Catmacey/ChipStomp/Bootloader/BoardConfig.h

/************************************************************************/
/*                                                                      */
/*    BoardConfig.h   This configures board specific features           */
/*                  for the stk500v2 avrdude/MPIDE PIC32                */
/*                    compliment bootloader                             */
/*                                                                      */
/************************************************************************/
/*    Author:     Keith Vogel                                           */
/*  Copyright 2013, Digilent Inc.                                       */
/************************************************************************/
/*
*
* Copyright (c) 2013-2014, Digilent <www.digilentinc.com>
* Contact Digilent for the latest version.
*
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
* THIS SOFTWARE IS PROVIDED BY THE COPYRIGHT HOLDERS AND CONTRIBUTORS "AS IS" AND
* ANY EXPRESS OR IMPLIED WARRANTIES, INCLUDING, BUT NOT LIMITED TO, THE IMPLIED
* WARRANTIES OF MERCHANTABILITY AND FITNESS FOR A PARTICULAR PURPOSE ARE DISCLAIMED.
* IN NO EVENT SHALL THE COPYRIGHT OWNER OR CONTRIBUTORS BE LIABLE FOR ANY DIRECT,
* INDIRECT, INCIDENTAL, SPECIAL, EXEMPLARY, OR CONSEQUENTIAL DAMAGES (INCLUDING,
* BUT NOT LIMITED TO, PROCUREMENT OF SUBSTITUTE GOODS OR SERVICES; LOSS OF USE,
* DATA, OR PROFITS; OR BUSINESS INTERRUPTION) HOWEVER CAUSED AND ON ANY THEORY OF
* LIABILITY, WHETHER IN CONTRACT, STRICT LIABILITY, OR TORT (INCLUDING NEGLIGENCE
* OR OTHERWISE) ARISING IN ANY WAY OUT OF THE USE OF THIS SOFTWARE, EVEN IF ADVISED
* OF THE POSSIBILITY OF SUCH DAMAGE.
*/
/************************************************************************/
/*  Revision History:                                                   */
/*                                                                      */
/*    2/23/2011(KeithV): Created                                        */
/*    6/17/2012(KeithV): Added Just In Time Flash Erase                 */
/*    6/17/2012(KeithV): Added header information                       */
/*    6/25/2012(KeithV): Added Vendor ID and Product IDs                */
/*    1/15/2013(BrianS): Added PPS unlock for MX1/MX2 devices           */
/*    3/18/2013(BrianS): Added 48Mhz FB Mini device, fixed USBID and    */
/*                       VBUSON                                         */
/*    22/5/2013(gmtii):  Added Olimex PIC32 Pinguino board		        */
/*    6/2302/13(BrianS): Added DP32                                     */
/*    1/15/2014 (KeithV): Added MZ support                              */
/*                                                                      */
/************************************************************************/

// *****************************************************************************
// *****************************************************************************
//                     Helper Macros
// *****************************************************************************
// *****************************************************************************
#define CAT1_2(a,b)         a##b
#define CAT_2(a,b)          CAT1_2(a,b)
#define CAT_3(a,b,c)        CAT_2(CAT_2(a,b),c)
#define CAT_4(a,b,c,d)      CAT_2(CAT_2(a,b),CAT_2(c,d))
#define CAT_5(a,b,c,d,e)    CAT_2(CAT_3(a,b,c),CAT_2(d,e))
#define Low     0
#define High    1

// *****************************************************************************
// *****************************************************************************
//                     Vendor IDs
// *****************************************************************************
// *****************************************************************************
#define     vendUnknown         0xFFFF
#define     vendUnassigned      0x0000
#define     vendDigilent        0x0001
#define     vendMicrochip       0x0002
#define     vendFubarino        0x0003
#define     vendSchmalzHausLLC  0x0004
#define     vendOlimex          0x0005
#define		vendElement14		0x0006
#define     vendPontech         0x0007
#define     vendExperimental    0x8000

// *****************************************************************************
// *****************************************************************************
//                    Digilent Product IDs
// *****************************************************************************
// *****************************************************************************
#define     prodUnknown         0xFFFF
#define     prodUnassigned      0x0000

// Hardware / software Arduino compatible chipKITs
#define     prodChipKITUno32    0x0101
#define     prodChipKITMax32    0x0102
#define     prodChipKITuC32     0x0103
#define     prodChipKITWF32     0x0104
#define     prodChipKITFG32     0x0105

// Cerebot like boards, only software Arduino compatible chipKITs
#define     prodCerebot32MX4    0x0201
#define     prodCerebot32MX7    0x0202
#define     prodCerebotMX3cK128 0x0203
#define     prodCerebotMX4cK    0x0204
#define     prodCerebotMX7cK    0x0205
#define     prodCerebotMX3cK512 0x0206

// DIP form factor, only software Arduino compatible chipKITs
#define     prodCmodCK1         0x0301

// Experimenter boards form factor, only software Arduino compatible chipKITs
#define     prodChipKITDP32     0x0401

// UDB board
#define     prodChipKITUDB32PIM 0x0501

// MZ processors
#define     prodChipKITWiFire   0x0601
#define     prodChipKITzUno     0x0602


// *****************************************************************************
// *****************************************************************************
//                    Fubarino Product IDs
// *****************************************************************************
// *****************************************************************************
#define     prodFubarinoSD      0x0001
#define     prodFubarinoMini    0x0002
#define     prodFubarinoSD_512K 0x0003
#define     prodFubarinoMini48MHz 0x0004
#define     prodFubarinoMini50MHz 0x0005

// *****************************************************************************
// *****************************************************************************
//                    Schmalz Haus Product IDs
// *****************************************************************************
// *****************************************************************************
#define     prodEBBv3      		0x0001
#define     prodUBW32MX460 		0x0002
#define     prodUBW32MX795 		0x0003

// *****************************************************************************
// *****************************************************************************
//                    Olimex Product IDs
// *****************************************************************************
// *****************************************************************************
#define     prodOlimex_PIC32_Pinguino   0x0001
#define     prodOlimex_Duinomite        0x0002

// *****************************************************************************
// *****************************************************************************
//                    Element14 Product IDs
// *****************************************************************************
// *****************************************************************************
#define     prodChipkitPi		0x0001

// *****************************************************************************
// *****************************************************************************
//                    Pontech Product IDs
// *****************************************************************************
// *****************************************************************************
#define     prodQuick240                0x0001

// Bootloader Capability bits
// The first 4 bits define what type of STK500 interface is used
// The next 4 bits define what LEDs are used
// The next 8 bits define how the bootloader is to be put in programming/listen mode
// The next 8 bits are how flash is erased instructed by the linker
// The next 4 bits are this and that capabilities instructed by the linker
// The last 4 bits are this and that capabilities
#define blCapUARTInterface                              0x00000001ul        // Avrdude talks over a UART
#define blCapUSBInterface                               0x00000002ul        // Avrdude talks over the USB for serial
#define blCapBootLED                                    0x00000010ul        // A boot LED is driven
#define blCapDownloadLED                                0x00000020ul        // A download LED is driven
#define blCapAutoResetListening                         0x00000100ul        // There is a short listening delay after reset for avrdude to upload a sketch before automatically loading the in flash sketch              
#define blCapProgramButton                              0x00000200ul        // A program button is suppored  
#define blCapVirtualProgramButton                       0x00000400ul        // A virtual program button is suppored
#define blCapLkInstrFullFlashEraseLess4KEEProm          0x00010000ul        // The original bootloader method of erasing all of program flash except the last 4K reserved for eeprom
#define blCapLkInstrJustInTimeFlashErase                0x00020000ul        // Only flash pages written too needed by the sketch is erased
#define blCapLkInstrFlashErase                          0x00040000ul        // The linker defines the flash range to erase
#define blCapLkInstrFullFlashErase                      0x00080000ul        // All of flash is erased
#define blCapLkInstrExecutionJumpAddress                0x01000000ul        // the bootloader will jump to the execution jump address immediately after programming
#define blCapLkInstrExecutionJumpToFirstInFlash         0x02000000ul        // the bootloader will jump to the first sketch loaded in flash ignoring the execution jump address immediately after programming
#define blCapSupportsRamHeaderAndPersistentData         0x10000000ul        // This checks and clears the Ram Header and adds RAM header data like the RCON value
#define blCapSplitFlashBootloader                       0x20000000ul        // This is a split flash bootloader with some of the bootloader in program flash
#define blCapSmartStart                                 0x40000000ul        // To indicate that the bootloader has implemented a smart start sequence to prevent execution of the sketch until all start sequences have stabalized.
#define blCapNotProvided                                0x80000000ul        // If this is set, then all capability bits have no meaning. This will be set if flash is in its erased state and the bootloader did not set any bits.

#define CAPCOMMON (blCapLkInstrFullFlashEraseLess4KEEProm | blCapLkInstrJustInTimeFlashErase | blCapLkInstrFlashErase | blCapLkInstrFullFlashErase | blCapLkInstrExecutionJumpAddress | blCapLkInstrExecutionJumpToFirstInFlash | blCapSupportsRamHeaderAndPersistentData)

#if !defined(__PIC32MX__) && !defined(__PIC32MZ__)
    #error "This project was designed for PIC32MX family devices. Please select the appropriate project for your target device family."
#endif

// For historical reasons, these must be defined as these specific constants and nothing else
#define FLASH_START             0x9D000000
#define USER_APP_ADDR           0x9D001000
#define DEFAULT_EEPROM_SIZE     4096

//************************************************************************
#if defined(_BOARD_EXAMPLE_MX1_)               

#if defined(PUT_CONFIG_BITS_HERE)

    //*    Oscillator Settings
    #pragma config FNOSC    = PRIPLL                        // Oscillator Selection
    #pragma config POSCMOD  = XT                            // Primary Oscillator
    #pragma config FPLLIDIV = DIV_2                         // PLL input divider
    #pragma config FPLLMUL  = MUL_20                        // PLL multiplier
    #pragma config FPLLODIV = DIV_2                         // PLL output divider
    #pragma config FPBDIV   = DIV_1                         // Peripheral bus clock divider
    #pragma config FSOSCEN  = OFF                           // Secondary Oscillator Enable

    //*    Clock control settings
    #pragma config IESO     = ON                            // Internal/External Switch-over
    #pragma config FCKSM    = CSDCMD                        // Clock Switching & Fail Safe Clock Monitor
    #pragma config OSCIOFNC = OFF                           // CLKO Enable

    //*    Other Peripheral Device settings
    #pragma config FWDTEN   = OFF                           // Watchdog Timer
    #pragma config WDTPS    = PS1024                        // Watchdog Timer Postscale
    #pragma config WINDIS   = OFF
    #pragma config JTAGEN   = OFF                           // JTAG port disabled

    //*    Code Protection settings
    #pragma config CP       = OFF                           // Code Protect
    #pragma config BWP      = OFF                           // Boot Flash Write Protect
    #pragma config PWP      = OFF                           // Program Flash Write Protect

    //*    Debug settings
    #pragma config ICESEL   = ICS_PGx1                      // ICE/ICD Comm Channel Select
    //#pragma config DEBUG    = ON                          // DO NOT SET THIS CONFIG BIT, it will break debugging

    #pragma config PMDL1WAY = OFF                           // Allow multiple reconfigurations
    #pragma config IOL1WAY  = OFF                           // Allow multiple reconfigurations
#endif

    #define CAPABILITIES    (blCapBootLED | blCapDownloadLED | blCapUARTInterface | blCapProgramButton | blCapVirtualProgramButton | CAPCOMMON)

    // BTN / LED sense
    #define LedOn       High
    #define BntOn       High

    // Boot LED
    #define BLedLat     A
    #define BLedBit     7

    // Download LED
    #define DLedLat     A
    #define DLedBit     8

    // Virtual program button
    #define VPBntLat    A
    #define VPBntBit    4

    // Program button
    #define PBntPort    A
    #define PBntBit     4

    #define _CPU_NAME_              "32MX120F032D"
    #define VEND                    vendUnassigned
    #define PROD                    prodUnassigned
    #define F_CPU                   40000000UL              // CPU frequence
    #define F_PBUS                  F_CPU                   // Peripheral bus rate F_CPU / FPBDIV; just set it, saves code.

    #define FLASH_BYTES             0x8000                  // 32K
    #define FLASH_PAGE_SIZE         1024

    #define BOOTLOADER_UART         1                       // avrdude program UART
    #define BAUDRATE                115200                  // avrdude baudrate
    #define UARTMapRX()             (U1RXR = 0x1)           // RPB6 -> U1RX
    #define UARTMapTX()             (RPB7R = 0x1)           // RB7 -> U1TX
 
//************************************************************************
#elif defined(_BOARD_UDB32_MX2_DIP_)

#if defined(PUT_CONFIG_BITS_HERE)

    //* Oscillator Settings
    #pragma config FNOSC    = PRIPLL                                // Oscillator selection
    #pragma config POSCMOD  = XT                                    // Primary oscillator mode
    #pragma config FPLLIDIV = DIV_2                                 // PLL input divider
    #pragma config FPLLMUL  = MUL_20                                // PLL multiplier
    #pragma config FPLLODIV = DIV_2                                 // PLL output divider
    #pragma config FPBDIV   = DIV_1                                 // Peripheral bus clock divider
    #pragma config FSOSCEN  = OFF                                    // Secondary oscillator enable

    //* Clock control settings
    #pragma config IESO     = OFF                                   // Internal/external clock switchover
    #pragma config FCKSM    = CSECME                                // Clock switching (CSx)/Clock monitor (CMx)
    #pragma config OSCIOFNC = OFF                                   // Clock output on OSCO pin enable

    //* USB Settings
    #pragma config UPLLEN   = ON                                    // USB PLL enable
    #pragma config UPLLIDIV = DIV_2                                 // USB PLL input divider
    #pragma config FVBUSONIO = OFF                                  // Make VBUSON a GPIO pin
    #pragma config FUSBIDIO = OFF                                   // Controlled by port function

    //* Other Peripheral Device settings
    #pragma config FWDTEN   = OFF                                   // Watchdog timer enable
    #pragma config WDTPS    = PS1024                                // Watchdog timer postscaler
    #pragma config WINDIS   = OFF
    #pragma config JTAGEN   = OFF                                   // JTAG port disabled

    //* Code Protection settings
    #pragma config CP       = OFF                                   // Code protection
    #pragma config BWP      = OFF                                   // Boot flash write protect
    #pragma config PWP      = OFF                                   // Program flash write protect

    //*    Debug settings
    #pragma config ICESEL   = ICS_PGx1                      		// ICE/ICD Comm Channel Select
    //#pragma config DEBUG    = ON                          		// DO NOT SET THIS CONFIG BIT, it will break debugging

    #pragma config PMDL1WAY = OFF                           		// Allow multiple reconfigurations
    #pragma config IOL1WAY  = OFF                           		// Allow multiple reconfigurations
#endif

    #define CAPABILITIES    (blCapBootLED | blCapDownloadLED | blCapUARTInterface | blCapProgramButton | blCapVirtualProgramButton | CAPCOMMON)

    // BTN / LED sense
    #define LedOn       Low
    #define BntOn       High

    // Boot LED
    #define BLedLat     B
    #define BLedBit     0

    // Download LED
    #define DLedLat     B
    #define DLedBit     1

    // Virtual program button
    #define VPBntLat    B
    #define VPBntBit    4

    // Program button
    #define PBntPort    B
    #define PBntBit     4

    #define _CPU_NAME_                  "32MX250F128B"
    #define VEND                        vendDigilent
    #define PROD                        prodChipKITDP32
    #define F_CPU                       40000000UL
    #define F_PBUS                      F_CPU

    #define FLASH_BYTES                 (0x20000)           // Leave room 4 pages (for bootloader!)
    #define FLASH_PAGE_SIZE             1024                // In bytes

    #define BOOTLOADER_UART             1                   // avrdude program UART
    #define BAUDRATE                    115200              // avrdude baudrate
    #define UARTMapRX()                 (U1RXR = 0x3)       // RPB13 -> U1RX
    #define UARTMapTX()                 (RPB3R = 0x1)       // RB3 -> U1TX

//************************************************************************
#elif defined(_BOARD_CMOD_CK1_)

#if defined(PUT_CONFIG_BITS_HERE)

    //*    Oscillator Settings
    #pragma config FNOSC    = PRIPLL                        // Oscillator Selection
    #pragma config POSCMOD  = XT                            // Primary Oscillator
    #pragma config FPLLIDIV = DIV_2                         // PLL input divider
    #pragma config FPLLMUL  = MUL_20                        // PLL multiplier
    #pragma config FPLLODIV = DIV_2                         // PLL output divider
    #pragma config FPBDIV   = DIV_1                         // Peripheral bus clock divider
    #pragma config FSOSCEN  = OFF                           // Secondary Oscillator Enable

    //*    Clock control settings
    #pragma config IESO     = ON                            // Internal/External Switch-over
    #pragma config FCKSM    = CSDCMD                        // Clock Switching & Fail Safe Clock Monitor
    #pragma config OSCIOFNC = OFF                           // CLKO Enable

    //*    Other Peripheral Device settings
    #pragma config FWDTEN   = OFF                           // Watchdog Timer
    #pragma config WDTPS    = PS1024                        // Watchdog Timer Postscale
    #pragma config WINDIS   = OFF
    #pragma config JTAGEN   = OFF                           // JTAG port disabled

    //*    Code Protection settings
    #pragma config CP       = OFF                           // Code Protect
    #pragma config BWP      = OFF                           // Boot Flash Write Protect
    #pragma config PWP      = OFF                           // Program Flash Write Protect

    //*    Debug settings
    #pragma config ICESEL   = ICS_PGx2                      // ICE/ICD Comm Channel Select
    //#pragma config DEBUG    = ON                          // DO NOT SET THIS CONFIG BIT, it will break debugging

    #pragma config PMDL1WAY = OFF                           // Allow multiple reconfigurations
    #pragma config IOL1WAY  = OFF                           // Allow multiple reconfigurations
#endif

    #define CAPABILITIES    (blCapBootLED | blCapDownloadLED | blCapUARTInterface | blCapAutoResetListening | blCapVirtualProgramButton | CAPCOMMON)

    // BTN / LED sense
    #define LedOn       High
    #define BntOn       High

    // Boot LED
    #define BLedLat     A
    #define BLedBit     10

    // Download LED
    #define DLedLat     B
    #define DLedBit     12

    // Virtual program button
    #define VPBntLat    A
    #define VPBntBit    2

    #define _CPU_NAME_              "PIC32MX150F128D"
    #define VEND                    vendDigilent
    #define PROD                    prodCmodCK1
    #define F_CPU                   40000000UL              // CPU frequence
    #define F_PBUS                  F_CPU                   // Peripheral bus rate F_CPU / FPBDIV; just set it, saves code.

    #define FLASH_BYTES             0x20000                  // 128K
    #define FLASH_PAGE_SIZE         1024

    #define LISTEN_BEFORE_LOAD      2000                    // no less than 2 seconds
    #define BOOTLOADER_UART         1                       // avrdude program UART
    #define BAUDRATE                115200                  // avrdude baudrate
    #define UARTMapRX()             (U1RXR = 0x5)           // RPC6 -> U1RX
    #define UARTMapTX()             (RPB3R = 0x1)           // RPB3 -> U1TX

//************************************************************************
#elif defined(_BOARD_CHIPKIT_DP32_)

#if defined(PUT_CONFIG_BITS_HERE)

    //* Oscillator Settings
    #pragma config FNOSC    = PRIPLL                                // Oscillator selection
    #pragma config POSCMOD  = XT                                    // Primary oscillator mode
    #pragma config FPLLIDIV = DIV_2                                 // PLL input divider
    #pragma config FPLLMUL  = MUL_20                                // PLL multiplier
    #pragma config FPLLODIV = DIV_2                                 // PLL output divider
    #pragma config FPBDIV   = DIV_1                                 // Peripheral bus clock divider
    #pragma config FSOSCEN  = OFF                                    // Secondary oscillator enable

    //* Clock control settings
    #pragma config IESO     = OFF                                   // Internal/external clock switchover
    #pragma config FCKSM    = CSECME                                // Clock switching (CSx)/Clock monitor (CMx)
    #pragma config OSCIOFNC = OFF                                   // Clock output on OSCO pin enable

    //* USB Settings
    #pragma config UPLLEN   = ON                                    // USB PLL enable
    #pragma config UPLLIDIV = DIV_2                                 // USB PLL input divider
    #pragma config FVBUSONIO = OFF                                  // Make VBUSON a GPIO pin
    #pragma config FUSBIDIO = OFF                                   // Controlled by port function

    //* Other Peripheral Device settings
    #pragma config FWDTEN   = OFF                                   // Watchdog timer enable
    #pragma config WDTPS    = PS1024                                // Watchdog timer postscaler
    #pragma config WINDIS   = OFF
    #pragma config JTAGEN   = OFF                                   // JTAG port disabled

    //* Code Protection settings
    #pragma config CP       = OFF                                   // Code protection
    #pragma config BWP      = OFF                                   // Boot flash write protect
    #pragma config PWP      = OFF                                   // Program flash write protect

    //*    Debug settings
    #pragma config ICESEL   = ICS_PGx1                      		// ICE/ICD Comm Channel Select
    //#pragma config DEBUG    = ON                          		// DO NOT SET THIS CONFIG BIT, it will break debugging

    #pragma config PMDL1WAY = OFF                           		// Allow multiple reconfigurations
    #pragma config IOL1WAY  = OFF                           		// Allow multiple reconfigurations
#endif

    #define CAPABILITIES    (blCapBootLED | blCapDownloadLED | blCapSplitFlashBootloader | blCapUSBInterface | blCapProgramButton | blCapVirtualProgramButton | CAPCOMMON)

    // BTN / LED sense
    #define LedOn       High
    #define BntOn       High

    // Boot LED
    #define BLedLat     B
    #define BLedBit     3

    // Download LED
    #define DLedLat     B
    #define DLedBit     2

    // Virtual program button
    #define VPBntLat    B
    #define VPBntBit    4

    // Program button
    #define PBntPort    B
    #define PBntBit     4

    #define _CPU_NAME_                  "32MX250F128B"
    #define VEND                        vendDigilent
    #define PROD                        prodChipKITDP32
    #define F_CPU                       40000000UL
    #define F_PBUS                      F_CPU

    #define FLASH_BYTES                 (0x20000-0x1000)		    // Leave room 4 pages (for bootloader!)
    #define FLASH_PAGE_SIZE             1024                                // In bytes

//************************************************************************
#elif defined(_BOARD_CHIPKIT_DP32_CHIPSTOMP_)

#if defined(PUT_CONFIG_BITS_HERE)

    //* Oscillator Settings
    #pragma config FNOSC    = PRIPLL                                // Oscillator selection
    #pragma config POSCMOD  = XT                                    // Primary oscillator mode
    #pragma config FPLLIDIV = DIV_2                                 // PLL input divider
    #pragma config FPLLMUL  = MUL_20                                // PLL multiplier
    #pragma config FPLLODIV = DIV_2                                 // PLL output divider
    #pragma config FPBDIV   = DIV_1                                 // Peripheral bus clock divider
    #pragma config FSOSCEN  = OFF                                    // Secondary oscillator enable

    //* Clock control settings
    #pragma config IESO     = OFF                                   // Internal/external clock switchover
    #pragma config FCKSM    = CSECME                                // Clock switching (CSx)/Clock monitor (CMx)
    #pragma config OSCIOFNC = OFF                                   // Clock output on OSCO pin enable

    //* USB Settings
    #pragma config UPLLEN   = ON                                    // USB PLL enable
    #pragma config UPLLIDIV = DIV_2                                 // USB PLL input divider
    #pragma config FVBUSONIO = OFF                                  // Make VBUSON a GPIO pin
    #pragma config FUSBIDIO = OFF                                   // Controlled by port function

    //* Other Peripheral Device settings
    #pragma config FWDTEN   = OFF                                   // Watchdog timer enable
    #pragma config WDTPS    = PS1024                                // Watchdog timer postscaler
    #pragma config WINDIS   = OFF
    #pragma config JTAGEN   = OFF                                   // JTAG port disabled

    //* Code Protection settings
    #pragma config CP       = OFF                                   // Code protection
    #pragma config BWP      = OFF                                   // Boot flash write protect
    #pragma config PWP      = OFF                                   // Program flash write protect

    //*    Debug settings
    #pragma config ICESEL   = ICS_PGx1                              // ICE/ICD Comm Channel Select
    //#pragma config DEBUG    = ON                                  // DO NOT SET THIS CONFIG BIT, it will break debugging

    #pragma config PMDL1WAY = OFF                                   // Allow multiple reconfigurations
    #pragma config IOL1WAY  = OFF                                   // Allow multiple reconfigurations
#endif

    #define CAPABILITIES    (blCapBootLED | blCapDownloadLED | blCapSplitFlashBootloader | blCapUSBInterface | blCapProgramButton | blCapVirtualProgramButton | CAPCOMMON)

    // BTN / LED sense
    #define LedOn       High
    #define BntOn       Low

    // Boot LED
    #define BLedLat     B
    #define BLedBit     3

    // Download LED
    #define DLedLat     B
    #define DLedBit     2

    // Virtual program button
    #define VPBntLat    B
    #define VPBntBit    4

    // Program button
    #define PBntPort    B
    #define PBntBit     4

    #define _CPU_NAME_                  "32MX250F128B"
    #define VEND                        vendDigilent
    #define PROD                        prodChipKITDP32
    #define F_CPU                       40000000UL
    #define F_PBUS                      F_CPU

    #define FLASH_BYTES                 (0x20000-0x1000)            // Leave room 4 pages (for bootloader!)
    #define FLASH_PAGE_SIZE             1024                                // In bytes

//************************************************************************
#elif defined(_BOARD_CHIPKIT_UNO32_)

#if defined(PUT_CONFIG_BITS_HERE)

    //*    Oscillator Settings
    #pragma config FNOSC    = PRIPLL                        // Oscillator selection
    #pragma config POSCMOD  = XT                            // Primary oscillator mode
    #pragma config FPLLIDIV = DIV_2                         // PLL input divider
    #pragma config FPLLMUL  = MUL_20                        // PLL multiplier
    #pragma config FPLLODIV = DIV_1                         // PLL output divider
    #pragma config FPBDIV   = DIV_1                         // Peripheral bus clock divider
    #pragma config FSOSCEN  = ON                            // Secondary oscillator enable

    //*    Clock control settings
    #pragma config IESO     = OFF                           // Internal/external clock switchover
    #pragma config FCKSM    = CSDCMD                        // Clock switching (CSx)/Clock monitor (CMx)
    #pragma config OSCIOFNC = OFF                           // Clock output on OSCO pin enable

    //*    Other Peripheral Device settings
    #pragma config FWDTEN   = OFF                           // Watchdog timer enable
    #pragma config WDTPS    =  PS1024                       // Watchdog timer postscaler

    //*    Code Protection settings
    #pragma config CP       = OFF                           // Code protection
    #pragma config BWP      = OFF                           // Boot flash write protect
    #pragma config PWP      = OFF                           // Program flash write protect

    //*    Debug settings
    #pragma config ICESEL   = ICS_PGx2                      // ICE pin selection
#endif

    #define CAPABILITIES    (blCapBootLED | blCapDownloadLED | blCapUARTInterface | blCapAutoResetListening | blCapVirtualProgramButton | CAPCOMMON)

    // BTN / LED sense
    #define LedOn       High
    #define BntOn       High

    // Boot LED
    #define BLedLat     G
    #define BLedBit     6

    // Download LED
    #define DLedLat     F
    #define DLedBit     0

    // Virtual program button
    #define VPBntLat    C
    #define VPBntBit    12

    // Other capabilities
    #define LISTEN_BEFORE_LOAD          2000                // no less than 2 seconds
    #define BOOTLOADER_UART             1                   // avrdude program UART
    #define BAUDRATE                    115200              // avrdude baudrate
 
    #define _CPU_NAME_                  "32MX320F128H"
    #define VEND                        vendDigilent
    #define PROD                        prodChipKITUno32
    #define F_CPU                       80000000UL
    #define F_PBUS                      F_CPU

    #define FLASH_BYTES                 0x20000             // 128K
    #define FLASH_PAGE_SIZE             4096
    #define LoadFlashWaitStates()       (CHECON = 2)

//************************************************************************
#elif defined(_BOARD_CEREBOT_MX3CK_128_)

#if defined(PUT_CONFIG_BITS_HERE)

    //*    Oscillator Settings
    #pragma config FNOSC    = PRIPLL                            // Oscillator selection
    #pragma config POSCMOD  = XT                                // Primary oscillator mode
    #pragma config FPLLIDIV = DIV_2                             // PLL input divider
    #pragma config FPLLMUL  = MUL_20                            // PLL multiplier
    #pragma config FPLLODIV = DIV_1                             // PLL output divider
    #pragma config FPBDIV   = DIV_1                             // Peripheral bus clock divider
    #pragma config FSOSCEN  = ON                                // Secondary oscillator enable

    //*    Clock control settings
    #pragma config IESO     = OFF                               // Internal/external clock switchover
    #pragma config FCKSM    = CSDCMD                            // Clock switching (CSx)/Clock monitor (CMx)
    #pragma config OSCIOFNC = OFF                               // Clock output on OSCO pin enable

    //*    Other Peripheral Device settings
    #pragma config FWDTEN   = OFF                               // Watchdog timer enable
    #pragma config WDTPS    = PS1024                            // Watchdog timer postscaler

    //*    Code Protection settings
    #pragma config CP       = OFF                               // Code protection
    #pragma config BWP      = OFF                               // Boot flash write protect
    #pragma config PWP      = OFF                               // Program flash write protect

    //*    Debug settings
    #pragma config ICESEL   = ICS_PGx2                          // ICE pin selection
#endif

    #define CAPABILITIES    (blCapBootLED | blCapDownloadLED | blCapUARTInterface | blCapAutoResetListening | blCapVirtualProgramButton | CAPCOMMON)

    // BTN / LED sense
    #define LedOn       High
    #define BntOn       High

    // Boot LED
    #define BLedLat     F
    #define BLedBit     0

    // Download LED
    #define DLedLat     F
    #define DLedBit     1

    // Virtual program button
    #define VPBntLat    C
    #define VPBntBit    12

    // Other capabilities
    #define LISTEN_BEFORE_LOAD          2000                // no less than 2 seconds
    #define BOOTLOADER_UART             1                   // avrdude program UART
    #define BAUDRATE                    115200              // avrdude baudrate
 
    #define _CPU_NAME_                  "32MX320F128H"
    #define VEND                        vendDigilent
    #define PROD                        prodCerebotMX3cK128
    #define F_CPU                       80000000UL
    #define F_PBUS                      F_CPU

    #define FLASH_BYTES                 0x20000             // 128K
    #define FLASH_PAGE_SIZE             4096
    #define LoadFlashWaitStates()       (CHECON = 2)        // 0 for 0-30Mhz, 1 for 31-60Mhz, 2 for 61-80Mhz

//************************************************************************
#elif defined(_BOARD_UDB32_PIM_)

#if defined(PUT_CONFIG_BITS_HERE)

    //*    Oscillator Settings
    #pragma config FNOSC    = PRIPLL                        // Oscillator selection
    #pragma config POSCMOD  = XT                            // Primary oscillator mode
    #pragma config FPLLIDIV = DIV_2                         // PLL input divider
    #pragma config FPLLMUL  = MUL_20                        // PLL multiplier
    #pragma config FPLLODIV = DIV_1                         // PLL output divider
    #pragma config FPBDIV   = DIV_1                         // Peripheral bus clock divider
    #pragma config FSOSCEN  = ON                            // Secondary oscillator enable

    //*    Clock control settings
    #pragma config IESO     = OFF                           // Internal/external clock switchover
    #pragma config FCKSM    = CSDCMD                        // Clock switching (CSx)/Clock monitor (CMx)
    #pragma config OSCIOFNC = OFF                           // Clock output on OSCO pin enable

    //*    Other Peripheral Device settings
    #pragma config FWDTEN   = OFF                           // Watchdog timer enable
    #pragma config WDTPS    = PS1024                        // Watchdog timer postscaler

    //*    Code Protection settings
    #pragma config CP       = OFF                           // Code protection
    #pragma config BWP      = OFF                           // Boot flash write protect
    #pragma config PWP      = OFF                           // Program flash write protect

    //*    Debug settings
    #pragma config ICESEL   = ICS_PGx1                      // ICE pin selection
#endif

    #define CAPABILITIES    (blCapBootLED | blCapDownloadLED | blCapUARTInterface | blCapProgramButton | blCapVirtualProgramButton | CAPCOMMON)

    // BTN / LED sense
    #define LedOn       Low
    #define BntOn       High

    // Boot LED
    #define BLedLat     A
    #define BLedBit     6

    // Download LED
    #define DLedLat     A
    #define DLedBit     7

    // Virtual program button
    #define VPBntLat    G
    #define VPBntBit    15

    // Program button
    #define PBntPort    G
    #define PBntBit     15

    // Other capabilities
    #define BOOTLOADER_UART             1                   // avrdude program UART
    #define BAUDRATE                    115200              // avrdude baudrate

    #define _CPU_NAME_                  "32MX360F512L"
    #define VEND                        vendDigilent
    #define PROD                        prodChipKITUDB32PIM
    #define F_CPU                       80000000UL
    #define F_PBUS                      F_CPU

    #define FLASH_BYTES                 0x80000         // 512K
    #define FLASH_PAGE_SIZE             4096
    #define LoadFlashWaitStates()       (CHECON = 2)

//************************************************************************
#elif defined(_BOARD_CHIPKIT_UC32_)

#if defined(PUT_CONFIG_BITS_HERE)

    //*    Oscillator Settings
    #pragma config FNOSC    = PRIPLL                        // Oscillator selection
    #pragma config POSCMOD  = XT                            // Primary oscillator mode
    #pragma config FPLLIDIV = DIV_2                         // PLL input divider
    #pragma config FPLLMUL  = MUL_20                        // PLL multiplier
    #pragma config FPLLODIV = DIV_1                         // PLL output divider
    #pragma config FPBDIV   = DIV_1                         // Peripheral bus clock divider
    #pragma config FSOSCEN  = ON                            // Secondary oscillator enable

    //*    Clock control settings
    #pragma config IESO     = OFF                           // Internal/external clock switchover
    #pragma config FCKSM    = CSDCMD                        // Clock switching (CSx)/Clock monitor (CMx)
    #pragma config OSCIOFNC = OFF                           // Clock output on OSCO pin enable

    //*    Other Peripheral Device settings
    #pragma config FWDTEN   = OFF                           // Watchdog timer enable
    #pragma config WDTPS    = PS1024                        // Watchdog timer postscaler

    //*    Code Protection settings
    #pragma config CP       = OFF                           // Code protection
    #pragma config BWP      = OFF                           // Boot flash write protect
    #pragma config PWP      = OFF                           // Program flash write protect

    //*    Debug settings
    #pragma config ICESEL   = ICS_PGx2                      // ICE pin selection
#endif

    #define CAPABILITIES    (blCapBootLED | blCapDownloadLED | blCapUARTInterface | blCapAutoResetListening | blCapVirtualProgramButton | CAPCOMMON)

    // BTN / LED sense
    #define LedOn       High
    #define BntOn       High

    // Boot LED
    #define BLedLat     G
    #define BLedBit     6

    // Download LED
    #define DLedLat     F
    #define DLedBit     0

    // Virtual program button
    #define VPBntLat    C
    #define VPBntBit    12

    // Other capabilities
    #define LISTEN_BEFORE_LOAD          2000                // no less than 2 seconds
    #define BOOTLOADER_UART             1                   // avrdude program UART
    #define BAUDRATE                    115200              // avrdude baudrate

    #define _CPU_NAME_                  "32MX340F512H"
    #define VEND                        vendDigilent
    #define PROD                        prodChipKITuC32
    #define F_CPU                       80000000UL
    #define F_PBUS                      F_CPU

    #define FLASH_BYTES                 0x80000         // 512K   
    #define FLASH_PAGE_SIZE             4096
    #define LoadFlashWaitStates()       (CHECON = 2)

//************************************************************************
#elif defined(_BOARD_CEREBOT_MX3CK_512_)

#if defined(PUT_CONFIG_BITS_HERE)

    //*    Oscillator Settings
    #pragma config FNOSC    = PRIPLL                            // Oscillator selection
    #pragma config POSCMOD  = XT                                // Primary oscillator mode
    #pragma config FPLLIDIV = DIV_2                             // PLL input divider
    #pragma config FPLLMUL  = MUL_20                            // PLL multiplier
    #pragma config FPLLODIV = DIV_1                             // PLL output divider
    #pragma config FPBDIV   = DIV_1                             // Peripheral bus clock divider
    #pragma config FSOSCEN  = ON                                // Secondary oscillator enable

    //*    Clock control settings
    #pragma config IESO     = OFF                               // Internal/external clock switchover
    #pragma config FCKSM    = CSDCMD                            // Clock switching (CSx)/Clock monitor (CMx)
    #pragma config OSCIOFNC = OFF                               // Clock output on OSCO pin enable

    //*    Other Peripheral Device settings
    #pragma config FWDTEN   = OFF                               // Watchdog timer enable
    #pragma config WDTPS    = PS1024                            // Watchdog timer postscaler

    //*    Code Protection settings
    #pragma config CP       = OFF                               // Code protection
    #pragma config BWP      = OFF                               // Boot flash write protect
    #pragma config PWP      = OFF                               // Program flash write protect

    //*    Debug settings
    #pragma config ICESEL   = ICS_PGx2                          // ICE pin selection
#endif

    #define CAPABILITIES    (blCapBootLED | blCapDownloadLED | blCapUARTInterface | blCapAutoResetListening | blCapVirtualProgramButton | CAPCOMMON)

    // BTN / LED sense
    #define LedOn       High
    #define BntOn       High

    // Boot LED
    #define BLedLat     F
    #define BLedBit     0

    // Download LED
    #define DLedLat     F
    #define DLedBit     1

    // Virtual program button
    #define VPBntLat    C
    #define VPBntBit    12

    // Other capabilities
    #define LISTEN_BEFORE_LOAD          2000                // no less than 2 seconds
    #define BOOTLOADER_UART             1                   // avrdude program UART
    #define BAUDRATE                    115200              // avrdude baudrate
 
    #define _CPU_NAME_                  "32MX340F512H"
    #define VEND                        vendDigilent
    #define PROD                        prodCerebotMX3cK512
    #define F_CPU                       80000000UL
    #define F_PBUS                      F_CPU

    #define FLASH_BYTES                 0x80000         // 512K   
    #define FLASH_PAGE_SIZE             4096
    #define LoadFlashWaitStates()       (CHECON = 2)        // 0 for 0-30Mhz, 1 for 31-60Mhz, 2 for 61-80Mhz

//************************************************************************
#elif defined(_BOARD_CEREBOT_32MX4_)
 
#if defined(PUT_CONFIG_BITS_HERE)

    //* Oscillator Settings
    #pragma config FNOSC    = PRIPLL                                // Oscillator selection
    #pragma config POSCMOD  = XT                                    // Primary oscillator mode
    #pragma config FPLLIDIV = DIV_2                                 // PLL input divider
    #pragma config FPLLMUL  = MUL_20                                // PLL multiplier
    #pragma config FPLLODIV = DIV_1                                 // PLL output divider
    #pragma config FPBDIV   = DIV_1                                 // Peripheral bus clock divider
    #pragma config FSOSCEN  = ON                                    // Secondary oscillator enable
    
    //* Clock control settings
    #pragma config IESO     = OFF                                   // Internal/external clock switchover
    #pragma config FCKSM    = CSECME                                // Clock switching (CSx)/Clock monitor (CMx)
    #pragma config OSCIOFNC = OFF                                   // Clock output on OSCO pin enable
    
    //* USB Settings
    #pragma config UPLLEN   = ON                                    // USB PLL enable
    #pragma config UPLLIDIV = DIV_2                                 // USB PLL input divider
    
    //* Other Peripheral Device settings
    #pragma config FWDTEN   = OFF                                   // Watchdog timer enable
    #pragma config WDTPS    = PS1024                                // Watchdog timer postscaler
    
    //* Code Protection settings
    #pragma config CP       = OFF                                   // Code protection
    #pragma config BWP      = OFF                                   // Boot flash write protect
    #pragma config PWP      = OFF                                   // Program flash write protect
    
    //* Debug settings
    #pragma config ICESEL   = ICS_PGx2                              // ICE pin selection
#endif
    
    #define CAPABILITIES    (blCapBootLED | blCapDownloadLED | blCapUARTInterface | blCapProgramButton | blCapVirtualProgramButton | CAPCOMMON)

    // BTN / LED sense
    #define LedOn       High
    #define BntOn       High

    // Boot LED
    #define BLedLat     B
    #define BLedBit     10

    // Download LED
    #define DLedLat     B
    #define DLedBit     11

    // Virtual program button
    #define VPBntLat    C
    #define VPBntBit    12

    // Program button
    #define PBntPort    A
    #define PBntBit     6

     // Other capabilities
    #define BOOTLOADER_UART             1                   // avrdude program UART
    #define BAUDRATE                                115200              

    #define _CPU_NAME_                  "32MX460F512L"
    #define VEND                        vendDigilent
    #define PROD                        prodCerebot32MX4
    #define F_CPU                       80000000UL
    #define F_PBUS                      F_CPU

    #define FLASH_BYTES                 0x80000                 // 512K
    #define FLASH_PAGE_SIZE             4096
    #define LoadFlashWaitStates()       (CHECON = 2)            // 0 for 0-30Mhz, 1 for 31-60Mhz, 2 for 61-80Mhz

//************************************************************************
#elif defined(_BOARD_CEREBOT_32MX4_USB_)
 
#if defined(PUT_CONFIG_BITS_HERE)

    //* Oscillator Settings
    #pragma config FNOSC    = PRIPLL                                // Oscillator selection
    #pragma config POSCMOD  = XT                                    // Primary oscillator mode
    #pragma config FPLLIDIV = DIV_2                                 // PLL input divider
    #pragma config FPLLMUL  = MUL_20                                // PLL multiplier
    #pragma config FPLLODIV = DIV_1                                 // PLL output divider
    #pragma config FPBDIV   = DIV_1                                 // Peripheral bus clock divider
    #pragma config FSOSCEN  = ON                                    // Secondary oscillator enable
    
    //* Clock control settings
    #pragma config IESO     = OFF                                   // Internal/external clock switchover
    #pragma config FCKSM    = CSECME                                // Clock switching (CSx)/Clock monitor (CMx)
    #pragma config OSCIOFNC = OFF                                   // Clock output on OSCO pin enable
    
    //* USB Settings
    #pragma config UPLLEN   = ON                                    // USB PLL enable
    #pragma config UPLLIDIV = DIV_2                                 // USB PLL input divider
    
    //* Other Peripheral Device settings
    #pragma config FWDTEN   = OFF                                   // Watchdog timer enable
    #pragma config WDTPS    = PS1024                                // Watchdog timer postscaler
    
    //* Code Protection settings
    #pragma config CP       = OFF                                   // Code protection
    #pragma config BWP      = OFF                                   // Boot flash write protect
    #pragma config PWP      = OFF                                   // Program flash write protect
    
    //* Debug settings
    #pragma config ICESEL   = ICS_PGx2                              // ICE pin selection
#endif
    
    #define CAPABILITIES    (blCapBootLED | blCapDownloadLED | blCapUSBInterface | blCapProgramButton | blCapVirtualProgramButton | CAPCOMMON)

    // BTN / LED sense
    #define LedOn       High
    #define BntOn       High

    // Boot LED
    #define BLedLat     B
    #define BLedBit     10

    // Download LED
    #define DLedLat     B
    #define DLedBit     11

    // Virtual program button
    #define VPBntLat    C
    #define VPBntBit    12

    // Program button
    #define PBntPort    A
    #define PBntBit     6

    #define _CPU_NAME_                  "32MX460F512L"
    #define VEND                        vendDigilent
    #define PROD                        prodCerebot32MX4
    #define F_CPU                       80000000UL
    #define F_PBUS                      F_CPU

    #define FLASH_BYTES                 0x80000                     // 512K
    #define FLASH_PAGE_SIZE             4096
    #define LoadFlashWaitStates()       (CHECON = 2)                // 0 for 0-30Mhz, 1 for 31-60Mhz, 2 for 61-80Mhz

//************************************************************************
#elif defined(_BOARD_CEREBOT_MX4CK_)
 
#if defined(PUT_CONFIG_BITS_HERE)

    //* Oscillator Settings
    #pragma config FNOSC    = PRIPLL                                // Oscillator selection
    #pragma config POSCMOD  = XT                                    // Primary oscillator mode
    #pragma config FPLLIDIV = DIV_2                                 // PLL input divider
    #pragma config FPLLMUL  = MUL_20                                // PLL multiplier
    #pragma config FPLLODIV = DIV_1                                 // PLL output divider
    #pragma config FPBDIV   = DIV_1                                 // Peripheral bus clock divider
    #pragma config FSOSCEN  = ON                                    // Secondary oscillator enable
    
    //* Clock control settings
    #pragma config IESO     = OFF                                   // Internal/external clock switchover
    #pragma config FCKSM    = CSECME                                // Clock switching (CSx)/Clock monitor (CMx)
    #pragma config OSCIOFNC = OFF                                   // Clock output on OSCO pin enable
    
    //* USB Settings
    #pragma config UPLLEN   = ON                                    // USB PLL enable
    #pragma config UPLLIDIV = DIV_2                                 // USB PLL input divider
    
    //* Other Peripheral Device settings
    #pragma config FWDTEN   = OFF                                   // Watchdog timer enable
    #pragma config WDTPS    = PS1024                                // Watchdog timer postscaler
    
    //* Code Protection settings
    #pragma config CP       = OFF                                   // Code protection
    #pragma config BWP      = OFF                                   // Boot flash write protect
    #pragma config PWP      = OFF                                   // Program flash write protect
    
    //* Debug settings
    #pragma config ICESEL   = ICS_PGx2                              // ICE pin selection
#endif
    
    #define CAPABILITIES    (blCapBootLED | blCapDownloadLED | blCapUARTInterface | blCapAutoResetListening | blCapVirtualProgramButton | CAPCOMMON)

    // BTN / LED sense
    #define LedOn       High
    #define BntOn       High

    // Boot LED
    #define BLedLat     B
    #define BLedBit     10

    // Download LED
    #define DLedLat     B
    #define DLedBit     11

    // Virtual program button
    #define VPBntLat    C
    #define VPBntBit    12

    // Other capabilities
    #define LISTEN_BEFORE_LOAD          2000                // no less than 2 seconds
    #define BOOTLOADER_UART             1                   // avrdude program UART
    #define BAUDRATE                    115200              // avrdude baudrate

    #define _CPU_NAME_                  "32MX460F512L"
    #define VEND                        vendDigilent
    #define PROD                        prodCerebotMX4cK
    #define F_CPU                       80000000UL
    #define F_PBUS                      F_CPU

    #define FLASH_BYTES                 0x80000                 // 512K
    #define FLASH_PAGE_SIZE             4096
    #define LoadFlashWaitStates()       (CHECON = 2)            // 0 for 0-30Mhz, 1 for 31-60Mhz, 2 for 61-80Mhz

//************************************************************************
#elif defined(_BOARD_UBW32_MX460_USB_)

#if defined(PUT_CONFIG_BITS_HERE)

    //*    Oscillator Settings
    #pragma config FNOSC        = PRIPLL                            // Oscillator selection
    #pragma config POSCMOD      = XT                                // Primary oscillator mode
    #pragma config FPLLIDIV     = DIV_2                             // PLL input divider
    #pragma config FPLLMUL      = MUL_20                            // PLL multiplier
    #pragma config FPLLODIV     = DIV_1                             // PLL output divider
    #pragma config FPBDIV       = DIV_1                             // Peripheral bus clock divider
    #pragma config FSOSCEN      = OFF                               // Secondary oscillator enable

    //*    Clock control settings
    #pragma config IESO         = ON                                // Internal/external clock switchover
    #pragma config FCKSM        = CSDCMD                            // Clock switching (CSx)/Clock monitor (CMx)
    #pragma config OSCIOFNC     = OFF                               // Clock output on OSCO pin enable

    //*    Other Peripheral Device settings
    #pragma config FWDTEN       = OFF                               // Watchdog timer enable
    #pragma config WDTPS        = PS1024                            // Watchdog timer postscaler

    //*    Code Protection settings
    #pragma config CP           = OFF                               // Code protection
    #pragma config BWP          = OFF                               // Boot flash write protect
    #pragma config PWP          = OFF                               // Program flash write protect

    //*    Debug settings
    #pragma config ICESEL       = ICS_PGx2                          // ICE pin selection

    //*    USB Settings
    #pragma config UPLLEN       = ON                                // USB PLL enable
    #pragma config UPLLIDIV     = DIV_2                             // USB PLL input divider
#endif

    #define CAPABILITIES    (blCapBootLED | blCapDownloadLED | blCapUSBInterface | blCapProgramButton | blCapVirtualProgramButton | CAPCOMMON)

    // BTN / LED sense
    #define LedOn       High
    #define BntOn       Low

    // Boot LED
    #define BLedLat     E
    #define BLedBit     3

    // Download LED
    #define DLedLat     E
    #define DLedBit     2

    // Virtual program button
    #define VPBntLat    E
    #define VPBntBit    7

    // Program button
    #define PBntPort    E
    #define PBntBit     7

    #define _CPU_NAME_                  "32MX460F512L"
    #define VEND                        vendSchmalzHausLLC
    #define PROD                        prodUBW32MX460
    #define F_CPU                       80000000UL
    #define F_PBUS                      F_CPU

    #define FLASH_BYTES                 0x80000                     // 512K
    #define FLASH_PAGE_SIZE             4096
    #define LoadFlashWaitStates()       (CHECON = 2)                // 0 for 0-30Mhz, 1 for 31-60Mhz, 2 for 61-80Mhz

//************************************************************************
#elif defined(_BOARD_CHIPKIT_WF32_)

#if defined(PUT_CONFIG_BITS_HERE)

    //*    Oscillator Settings
    #pragma config FNOSC        = PRIPLL                            // Oscillator selection
    #pragma config POSCMOD      = XT                                // Primary oscillator mode
    #pragma config FPLLIDIV     = DIV_2                             // PLL input divider
    #pragma config FPLLMUL      = MUL_20                            // PLL multiplier
    #pragma config FPLLODIV     = DIV_1                             // PLL output divider
    #pragma config FPBDIV       = DIV_1                             // Peripheral bus clock divider
    #pragma config FSOSCEN      = OFF                               // Secondary oscillator enable

    //*    Clock control settings
    #pragma config IESO         = OFF                               // Internal/external clock switchover
    #pragma config FCKSM        = CSDCMD                            // Clock switching (CSx)/Clock monitor (CMx)
    #pragma config OSCIOFNC     = OFF                               // Clock output on OSCO pin enable

    //*    Other Peripheral Device settings
    #pragma config FWDTEN       = OFF                               // Watchdog timer enable
    #pragma config WDTPS        = PS1024                            // Watchdog timer postscaler

    //*    Code Protection settings
    #pragma config CP           = OFF                               // Code protection
    #pragma config BWP          = OFF                               // Boot flash write protect
    #pragma config PWP          = OFF                               // Program flash write protect

    //*    Debug settings
    #pragma config ICESEL       = ICS_PGx2                          // ICE pin selection

    //*    Other Peripheral Device settings
    #pragma config FSRSSEL      = PRIORITY_7                        // SRS interrupt priority
//    #pragma config FCANIO       = OFF                               // Standard/alternate CAN pin select (OFF=Alt)
    #pragma config FETHIO       = ON                                // Standard/alternate ETH pin select (OFF=Alt)
    #pragma config FMIIEN       = OFF                               // MII/RMII select (OFF=RMII)

    //*    USB Settings
    #pragma config UPLLEN       = ON                                // USB PLL enable
    #pragma config UPLLIDIV     = DIV_2                             // USB PLL input divider
    #pragma config FVBUSONIO    = OFF                               // VBUS pin control
    #pragma config FUSBIDIO     = OFF                               // USBID pin control
#endif

    #define CAPABILITIES    (blCapBootLED | blCapDownloadLED | blCapUARTInterface | blCapAutoResetListening | blCapVirtualProgramButton | CAPCOMMON)

    // BTN / LED sense
    #define LedOn       High
    #define BntOn       High

    // Boot LED
    #define BLedLat     G
    #define BLedBit     6

    // Download LED
    #define DLedLat     F
    #define DLedBit     0

    // Virtual program button
    #define VPBntLat    C
    #define VPBntBit    12

    // Other capabilities
    #define LISTEN_BEFORE_LOAD          2000                // no less than 2 seconds
    #define BOOTLOADER_UART             1                   // avrdude program UART
    #define BAUDRATE                    115200              // avrdude baudrate

    #define _CPU_NAME_                  "32MX695F512L"
    #define VEND                        vendDigilent
    #define PROD                        prodChipKITWF32
    #define F_CPU                       80000000UL
    #define F_PBUS                      F_CPU

    #define FLASH_BYTES                 0x80000                     // 512K
    #define FLASH_PAGE_SIZE             4096
    #define LoadFlashWaitStates()       (CHECON = 2)                // 0 for 0-30Mhz, 1 for 31-60Mhz, 2 for 61-80Mhz

//************************************************************************
#elif defined(_BOARD_CHIPKIT_ZUNO_)

#if defined(PUT_CONFIG_BITS_HERE)

     //*    Oscillator Settings
    // works with proper timing
    #pragma config POSCMOD      = EC                                // External Clock
//    #pragma config POSCMOD      = HS                                // Crystal

    #pragma config FPLLIDIV     = DIV_3                             // 8 MHz
    #pragma config FPLLICLK     = PLL_POSC                          // 8MHz Posc

    #pragma config FNOSC        = SPLL                              // Oscillator selection
    #pragma config FPLLMULT     = MUL_50                            // 400 MHz
    #pragma config FPLLODIV     = DIV_2                             // 200 MHz or 80 MHz, depending

    #pragma config FPLLRNG      = RANGE_5_10_MHZ                    // 5-10Mhz
    #pragma config FSOSCEN      = OFF                               // Secondary oscillator enable
    #pragma config UPLLFSEL     = FREQ_24MHZ                        // USB PLL Input Frequency Selection (USB PLL input is 24 MHz)

    //*    Clock control settings
    #pragma config IESO         = ON                                // Internal/external clock switchover
    #pragma config FCKSM        = CSDCMD                            // Clock switching (CSx)/Clock monitor (CMx)
    #pragma config OSCIOFNC     = OFF                               // Clock output on OSCO pin enable

    //*    Other Peripheral Device settings
    #pragma config FWDTEN       = OFF                               // Watchdog timer enable
    #pragma config WDTPS        = PS1048576                         // Watchdog timer postscaler
    #pragma config WDTSPGM      = STOP                              // Watchdog Timer Stop During Flash Programming (WDT stops during Flash programming)
    #pragma config WINDIS       = NORMAL          // Watchdog Timer Window Mode (Watchdog Timer is in non-Window mode)
    #pragma config FWDTWINSZ    = WINSZ_25     // Watchdog Timer Window Size (Window size is 25%)
    #pragma config FDMTEN       = OFF             // Deadman Timer Enable (Deadman Timer is disabled)

    //*    Code Protection settings
    #pragma config CP           = OFF                               // Code protection

    //*    Debug settings
//    #pragma config DEBUG       = ON                             // turn debugging on
    #pragma config ICESEL       = ICS_PGx2                          // ICE pin selection

    #pragma config FETHIO       = ON                                // Standard/alternate ETH pin select (OFF=Alt)
    #pragma config FMIIEN       = OFF                               // MII/RMII select (OFF=RMII)

    #pragma config BOOTISA  = MIPS32

    //*    USB Settings
    #pragma config UPLLEN       = ON                                // USB PLL enable
//    #pragma config UPLLIDIV     = DIV_2                             // USB PLL input divider
//    #pragma config FVBUSONIO    = OFF                               // VBUS pin control
    #pragma config FUSBIDIO     = OFF                               // USBID pin control

    #pragma config DMTCNT       = 0

//#pragma config PGL1WAY  = OFF             // Permission Group Lock One Way Configuration (Allow only one reconfiguration)
//#pragma config PMDL1WAY = OFF           // Peripheral Module Disable Configuration (Allow only one reconfiguration)
//#pragma config IOL1WAY  = OFF             // Peripheral Pin Select Configuration (Allow only one reconfiguration)
//#pragma config DMTINTV  = WIN_127_128    // DMT Count Window Interval (Window/Interval value is 127/128 counter value)
//#pragma config EJTAGBEN = NORMAL
//#pragma config DBGPER   = PG_ALL
//#pragma config FSLEEP   = OFF
//#pragma config FECCCON  = OFF_UNLOCKED
//#pragma config TRCEN    = OFF

#endif

    #define CAPABILITIES    (blCapBootLED | blCapDownloadLED | blCapUARTInterface | blCapAutoResetListening | blCapVirtualProgramButton | CAPCOMMON)

    // BTN / LED sense
    #define LedOn       High
    #define BntOn       High

    // Boot LED
    #define BLedLat     B
    #define BLedBit     14

    // Download LED
    #define DLedLat     B
    #define DLedBit     15

    // Virtual program button
    #define VPBntLat    C
    #define VPBntBit    12

    // Other capabilities
    #define LISTEN_BEFORE_LOAD          2000                // no less than 2 seconds
    #define BOOTLOADER_UART             1                   // avrdude program UART
    #define BAUDRATE                    115200              // avrdude baudrate
    #define UARTMapRX()                 (U1RXR = 0b0100)    // RPF1 -> U1RX
    #define UARTMapTX()                 (RPF0R = 0b0001)    // RF0 -> U1TX

    #define _CPU_NAME_                  "PIC32MZ2048ECG"
    #define VEND                        vendDigilent
    #define PROD                        prodChipKITzUno
    #define F_CPU                       200000000UL
    #define F_PBUS                      (F_CPU / (PB2DIVbits.PBDIV + 1))

    #define FLASH_BYTES                 0x200000                    // 2MB
    #define FLASH_PAGE_SIZE             0x4000                      // 16K

//************************************************************************
#elif defined(_BOARD_CHIPKIT_WIFIRE_)

#if defined(PUT_CONFIG_BITS_HERE)

     //*    Oscillator Settings
    // works with proper timing
    #pragma config POSCMOD      = EC                                // External Clock
//    #pragma config POSCMOD      = HS                                // Crystal

    #pragma config FPLLIDIV     = DIV_3                             // 8 MHz
    #pragma config FPLLICLK     = PLL_POSC                          // 8MHz Posc

    #pragma config FNOSC        = SPLL                              // Oscillator selection
    #pragma config FPLLMULT     = MUL_50                            // 400 MHz
    #pragma config FPLLODIV     = DIV_2                             // 200 MHz or 80 MHz, depending

    #pragma config FPLLRNG      = RANGE_5_10_MHZ                    // 5-10Mhz
    #pragma config FSOSCEN      = OFF                               // Secondary oscillator enable
    #pragma config UPLLFSEL     = FREQ_24MHZ                        // USB PLL Input Frequency Selection (USB PLL input is 24 MHz)

    //*    Clock control settings
    #pragma config IESO         = ON                                // Internal/external clock switchover
    #pragma config FCKSM        = CSDCMD                            // Clock switching (CSx)/Clock monitor (CMx)
    #pragma config OSCIOFNC     = OFF                               // Clock output on OSCO pin enable

    //*    Other Peripheral Device settings
    #pragma config FWDTEN       = OFF                               // Watchdog timer enable
    #pragma config WDTPS        = PS1048576                         // Watchdog timer postscaler
    #pragma config WDTSPGM      = STOP                              // Watchdog Timer Stop During Flash Programming (WDT stops during Flash programming)
    #pragma config WINDIS       = NORMAL                            // Watchdog Timer Window Mode (Watchdog Timer is in non-Window mode)
    #pragma config FWDTWINSZ    = WINSZ_25                          // Watchdog Timer Window Size (Window size is 25%)
    #pragma config FDMTEN       = OFF                               // Deadman Timer Enable (Deadman Timer is disabled)

    //*    Code Protection settings
    #pragma config CP           = OFF                               // Code protection

    //*    Debug settings
//    #pragma config DEBUG       = ON                               // turn debugging on
    #pragma config ICESEL       = ICS_PGx2                          // ICE pin selection

    #pragma config FETHIO       = ON                                // Standard/alternate ETH pin select (OFF=Alt)
    #pragma config FMIIEN       = OFF                               // MII/RMII select (OFF=RMII)

    #pragma config BOOTISA  = MIPS32

    //*    USB Settings
    #pragma config UPLLEN       = ON                                // USB PLL enable
    #pragma config FUSBIDIO     = OFF                               // USBID pin control

    #pragma config DMTCNT       = 0

//#pragma config PGL1WAY  = OFF             // Permission Group Lock One Way Configuration (Allow only one reconfiguration)
//#pragma config PMDL1WAY = OFF             // Peripheral Module Disable Configuration (Allow only one reconfiguration)
//#pragma config IOL1WAY  = OFF             // Peripheral Pin Select Configuration (Allow only one reconfiguration)
//#pragma config DMTINTV  = WIN_127_128     // DMT Count Window Interval (Window/Interval value is 127/128 counter value)
//#pragma config EJTAGBEN = NORMAL
//#pragma config DBGPER   = PG_ALL
//#pragma config FSLEEP   = OFF
//#pragma config FECCCON  = OFF_UNLOCKED
//#pragma config TRCEN    = OFF

#endif

    #define CAPABILITIES    (blCapBootLED | blCapDownloadLED | blCapUARTInterface | blCapAutoResetListening | blCapVirtualProgramButton | CAPCOMMON)

    // BTN / LED sense
    #define LedOn       High
    #define BntOn       High

    // Boot LED
    #define BLedLat     G
    #define BLedBit     6

    // Download LED
    #define DLedLat     D
    #define DLedBit     4

    // Virtual program button
    #define VPBntLat    C
    #define VPBntBit    12

    // Other capabilities
    #define LISTEN_BEFORE_LOAD          2000                // no less than 2 seconds
    #define BOOTLOADER_UART             4                   // avrdude program UART
    #define BAUDRATE                    115200              // avrdude baudrate
    #define UARTMapRX()                 (U4RXR = 0b1011)    // RPF2 -> U4RX
    #define UARTMapTX()                 (RPF8R = 0b0010)    // RF8 -> U4TX

    #define _CPU_NAME_                  "PIC32MZ2048ECG"
    #define VEND                        vendDigilent
    #define PROD                        prodChipKITWiFire
    #define F_CPU                       200000000UL
    #define F_PBUS                      (F_CPU / (PB2DIVbits.PBDIV + 1))

    #define FLASH_BYTES                 0x200000                    // 2MB
    #define FLASH_PAGE_SIZE             0x4000                      // 16K

//************************************************************************
#elif defined(_BOARD_CHIPKIT_MAX32_)

#if defined(PUT_CONFIG_BITS_HERE)

    //*    Oscillator Settings
    #pragma config FNOSC        = PRIPLL                            // Oscillator selection
    #pragma config POSCMOD      = XT                                // Primary oscillator mode
    #pragma config FPLLIDIV     = DIV_2                             // PLL input divider
    #pragma config FPLLMUL      = MUL_20                            // PLL multiplier
    #pragma config FPLLODIV     = DIV_1                             // PLL output divider
    #pragma config FPBDIV       = DIV_1                             // Peripheral bus clock divider
    #pragma config FSOSCEN      = OFF                               // Secondary oscillator enable

    //*    Clock control settings
    #pragma config IESO         = OFF                               // Internal/external clock switchover
    #pragma config FCKSM        = CSDCMD                            // Clock switching (CSx)/Clock monitor (CMx)
    #pragma config OSCIOFNC     = OFF                               // Clock output on OSCO pin enable

    //*    Other Peripheral Device settings
    #pragma config FWDTEN       = OFF                               // Watchdog timer enable
    #pragma config WDTPS        = PS1024                            // Watchdog timer postscaler

    //*    Code Protection settings
    #pragma config CP           = OFF                               // Code protection
    #pragma config BWP          = OFF                               // Boot flash write protect
    #pragma config PWP          = OFF                               // Program flash write protect

    //*    Debug settings
    #pragma config ICESEL       = ICS_PGx2                          // ICE pin selection

    //*    Other Peripheral Device settings
    #pragma config FSRSSEL      = PRIORITY_7                        // SRS interrupt priority
    #pragma config FCANIO       = OFF                               // Standard/alternate CAN pin select (OFF=Alt)
    #pragma config FETHIO       = ON                                // Standard/alternate ETH pin select (OFF=Alt)
    #pragma config FMIIEN       = OFF                               // MII/RMII select (OFF=RMII)

    //*    USB Settings
    #pragma config UPLLEN       = ON                                // USB PLL enable
    #pragma config UPLLIDIV     = DIV_2                             // USB PLL input divider
    #pragma config FVBUSONIO    = OFF                               // VBUS pin control
    #pragma config FUSBIDIO     = OFF                               // USBID pin control
#endif

    #define CAPABILITIES    (blCapBootLED | blCapDownloadLED | blCapUARTInterface | blCapAutoResetListening | blCapVirtualProgramButton | CAPCOMMON)

    // BTN / LED sense
    #define LedOn       High
    #define BntOn       High

    // Boot LED
    #define BLedLat     A
    #define BLedBit     3

    // Download LED
    #define DLedLat     C
    #define DLedBit     1

    // Virtual program button
    #define VPBntLat    C
    #define VPBntBit    12

    // Other capabilities
    #define LISTEN_BEFORE_LOAD          2000                // no less than 2 seconds
    #define BOOTLOADER_UART             1                   // avrdude program UART
    #define BAUDRATE                    115200              // avrdude baudrate

    #define _CPU_NAME_                  "32MX795F512L"
    #define VEND                        vendDigilent
    #define PROD                        prodChipKITMax32
    #define F_CPU                       80000000UL
    #define F_PBUS                      F_CPU

    #define FLASH_BYTES                 0x80000                     // 512K
    #define FLASH_PAGE_SIZE             4096
    #define LoadFlashWaitStates()       (CHECON = 2)                // 0 for 0-30Mhz, 1 for 31-60Mhz, 2 for 61-80Mhz

//************************************************************************
#elif defined(_BOARD_CEREBOT_32MX7_)

#if defined(PUT_CONFIG_BITS_HERE)

    //*    Oscillator Settings
    #pragma config FNOSC        = PRIPLL                            // Oscillator selection
    #pragma config POSCMOD      = XT                                // Primary oscillator mode
    #pragma config FPLLIDIV     = DIV_2                             // PLL input divider
    #pragma config FPLLMUL      = MUL_20                            // PLL multiplier
    #pragma config FPLLODIV     = DIV_1                             // PLL output divider
    #pragma config FPBDIV       = DIV_1                             // Peripheral bus clock divider
    #pragma config FSOSCEN      = OFF                               // Secondary oscillator enable

    //*    Clock control settings
    #pragma config IESO         = OFF                               // Internal/external clock switchover
    #pragma config FCKSM        = CSDCMD                            // Clock switching (CSx)/Clock monitor (CMx)
    #pragma config OSCIOFNC     = OFF                               // Clock output on OSCO pin enable

    //*    Other Peripheral Device settings
    #pragma config FWDTEN       = OFF                               // Watchdog timer enable
    #pragma config WDTPS        = PS1024                            // Watchdog timer postscaler

    //*    Code Protection settings
    #pragma config CP           = OFF                               // Code protection
    #pragma config BWP          = OFF                               // Boot flash write protect
    #pragma config PWP          = OFF                               // Program flash write protect

    //*    Debug settings
    #pragma config ICESEL       = ICS_PGx1                          // ICE pin selection

    //*    Other Peripheral Device settings
    #pragma config FSRSSEL      = PRIORITY_7                        // SRS interrupt priority
    #pragma config FCANIO       = OFF                               // Standard/alternate CAN pin select (OFF=Alt)
    #pragma config FETHIO       = ON                                // Standard/alternate ETH pin select (OFF=Alt)
    #pragma config FMIIEN       = OFF                               // MII/RMII select (OFF=RMII)

    //*    USB Settings
    #pragma config UPLLEN       = ON                                // USB PLL enable
    #pragma config UPLLIDIV     = DIV_2                             // USB PLL input divider
    #pragma config FVBUSONIO    = OFF                               // VBUS pin control
    #pragma config FUSBIDIO     = OFF                               // USBID pin control
#endif

    #define CAPABILITIES    (blCapBootLED | blCapDownloadLED | blCapUARTInterface | blCapProgramButton | blCapVirtualProgramButton | CAPCOMMON)

    // BTN / LED sense
    #define LedOn       High
    #define BntOn       High

    // Boot LED
    #define BLedLat     G
    #define BLedBit     12

    // Download LED
    #define DLedLat     G
    #define DLedBit     13

    // Virtual program button
    #define VPBntLat    C
    #define VPBntBit    12

    // Program button
    #define PBntPort    G
    #define PBntBit     6

    // Other capabilities
    #define BOOTLOADER_UART             1                   // avrdude program UART
    #define BAUDRATE                    115200              // avrdude baudrate

    #define _CPU_NAME_                  "32MX795F512L"
    #define VEND                        vendDigilent
    #define PROD                        prodCerebot32MX7
    #define F_CPU                       80000000UL
    #define F_PBUS                      F_CPU

    #define FLASH_BYTES                 0x80000                 // 512K
    #define FLASH_PAGE_SIZE             4096
    #define LoadFlashWaitStates()       (CHECON = 2)            // 0 for 0-30Mhz, 1 for 31-60Mhz, 2 for 61-80Mhz

//************************************************************************
#elif defined(_BOARD_CEREBOT_32MX7_USB_)

#if defined(PUT_CONFIG_BITS_HERE)

    //*    Oscillator Settings
    #pragma config FNOSC        = PRIPLL                            // Oscillator selection
    #pragma config POSCMOD      = XT                                // Primary oscillator mode
    #pragma config FPLLIDIV     = DIV_2                             // PLL input divider
    #pragma config FPLLMUL      = MUL_20                            // PLL multiplier
    #pragma config FPLLODIV     = DIV_1                             // PLL output divider
    #pragma config FPBDIV       = DIV_1                             // Peripheral bus clock divider
    #pragma config FSOSCEN      = OFF                               // Secondary oscillator enable

    //*    Clock control settings
    #pragma config IESO         = OFF                               // Internal/external clock switchover
    #pragma config FCKSM        = CSDCMD                            // Clock switching (CSx)/Clock monitor (CMx)
    #pragma config OSCIOFNC     = OFF                               // Clock output on OSCO pin enable

    //*    Other Peripheral Device settings
    #pragma config FWDTEN       = OFF                               // Watchdog timer enable
    #pragma config WDTPS        = PS1024                            // Watchdog timer postscaler

    //*    Code Protection settings
    #pragma config CP           = OFF                               // Code protection
    #pragma config BWP          = OFF                               // Boot flash write protect
    #pragma config PWP          = OFF                               // Program flash write protect

    //*    Debug settings
    #pragma config ICESEL       = ICS_PGx1                          // ICE pin selection

    //*    Other Peripheral Device settings
    #pragma config FSRSSEL      = PRIORITY_7                        // SRS interrupt priority
    #pragma config FCANIO       = OFF                               // Standard/alternate CAN pin select (OFF=Alt)
    #pragma config FETHIO       = ON                                // Standard/alternate ETH pin select (OFF=Alt)
    #pragma config FMIIEN       = OFF                               // MII/RMII select (OFF=RMII)

    //*    USB Settings
    #pragma config UPLLEN       = ON                                // USB PLL enable
    #pragma config UPLLIDIV     = DIV_2                             // USB PLL input divider
    #pragma config FVBUSONIO    = OFF                               // VBUS pin control
    #pragma config FUSBIDIO     = OFF                               // USBID pin control
#endif

    #define CAPABILITIES    (blCapBootLED | blCapDownloadLED | blCapUSBInterface | blCapProgramButton | blCapVirtualProgramButton | CAPCOMMON)

    // BTN / LED sense
    #define LedOn       High
    #define BntOn       High

    // Boot LED
    #define BLedLat     G
    #define BLedBit     12

    // Download LED
    #define DLedLat     G
    #define DLedBit     13

    // Virtual program button
    #define VPBntLat    C
    #define VPBntBit    12

    // Program button
    #define PBntPort    G
    #define PBntBit     6

    // Other capabilities
    #define BOOTLOADER_UART             1                   // avrdude program UART
    #define BAUDRATE                    115200              // avrdude baudrate

    #define _CPU_NAME_                  "32MX795F512L"
    #define VEND                        vendDigilent
    #define PROD                        prodCerebot32MX7
    #define F_CPU                       80000000UL
    #define F_PBUS                      F_CPU

    #define FLASH_BYTES                 0x80000                     // 512K
    #define FLASH_PAGE_SIZE             4096
    #define LoadFlashWaitStates()       (CHECON = 2)                // 0 for 0-30Mhz, 1 for 31-60Mhz, 2 for 61-80Mhz
 
//************************************************************************
#elif defined(_BOARD_CEREBOT_32MX7_USB_SPLIT_)

#if defined(PUT_CONFIG_BITS_HERE)

    //*    Oscillator Settings
    #pragma config FNOSC        = PRIPLL                            // Oscillator selection
    #pragma config POSCMOD      = XT                                // Primary oscillator mode
    #pragma config FPLLIDIV     = DIV_2                             // PLL input divider
    #pragma config FPLLMUL      = MUL_20                            // PLL multiplier
    #pragma config FPLLODIV     = DIV_1                             // PLL output divider
    #pragma config FPBDIV       = DIV_1                             // Peripheral bus clock divider
    #pragma config FSOSCEN      = OFF                               // Secondary oscillator enable

    //*    Clock control settings
    #pragma config IESO         = OFF                               // Internal/external clock switchover
    #pragma config FCKSM        = CSDCMD                            // Clock switching (CSx)/Clock monitor (CMx)
    #pragma config OSCIOFNC     = OFF                               // Clock output on OSCO pin enable

    //*    Other Peripheral Device settings
    #pragma config FWDTEN       = OFF                               // Watchdog timer enable
    #pragma config WDTPS        = PS1024                            // Watchdog timer postscaler

    //*    Code Protection settings
    #pragma config CP           = OFF                               // Code protection
    #pragma config BWP          = OFF                               // Boot flash write protect
    #pragma config PWP          = OFF                               // Program flash write protect

    //*    Debug settings
    #pragma config ICESEL       = ICS_PGx1                          // ICE pin selection

    //*    Other Peripheral Device settings
    #pragma config FSRSSEL      = PRIORITY_7                        // SRS interrupt priority
    #pragma config FCANIO       = OFF                               // Standard/alternate CAN pin select (OFF=Alt)
    #pragma config FETHIO       = ON                                // Standard/alternate ETH pin select (OFF=Alt)
    #pragma config FMIIEN       = OFF                               // MII/RMII select (OFF=RMII)

    //*    USB Settings
    #pragma config UPLLEN       = ON                                // USB PLL enable
    #pragma config UPLLIDIV     = DIV_2                             // USB PLL input divider
    #pragma config FVBUSONIO    = OFF                               // VBUS pin control
    #pragma config FUSBIDIO     = OFF                               // USBID pin control
#endif

    #define CAPABILITIES    (blCapBootLED | blCapDownloadLED | blCapUSBInterface | blCapProgramButton | blCapVirtualProgramButton | CAPCOMMON)

    // BTN / LED sense
    #define LedOn       High
    #define BntOn       High

    // Boot LED
    #define BLedLat     G
    #define BLedBit     12

    // Download LED
    #define DLedLat     G
    #define DLedBit     13

    // Virtual program button
    #define VPBntLat    C
    #define VPBntBit    12

    // Program button
    #define PBntPort    G
    #define PBntBit     6

    #define _CPU_NAME_                  "32MX795F512L"
    #define VEND                        vendDigilent
    #define PROD                        prodCerebot32MX7
    #define F_CPU                       80000000UL
    #define F_PBUS                      F_CPU

    #define FLASH_BYTES                 (0x80000-4096)              // 512K less 4K for the splitflash bootloader in program flash
    #define FLASH_PAGE_SIZE             4096
    #define LoadFlashWaitStates()       (CHECON = 2)                // 0 for 0-30Mhz, 1 for 31-60Mhz, 2 for 61-80Mhz
 
//************************************************************************
#elif defined(_BOARD_CEREBOT_MX7CK_)

#if defined(PUT_CONFIG_BITS_HERE)

    //*    Oscillator Settings
    #pragma config FNOSC        = PRIPLL                            // Oscillator selection
    #pragma config POSCMOD      = XT                                // Primary oscillator mode
    #pragma config FPLLIDIV     = DIV_2                             // PLL input divider
    #pragma config FPLLMUL      = MUL_20                            // PLL multiplier
    #pragma config FPLLODIV     = DIV_1                             // PLL output divider
    #pragma config FPBDIV       = DIV_1                             // Peripheral bus clock divider
    #pragma config FSOSCEN      = OFF                               // Secondary oscillator enable

    //*    Clock control settings
    #pragma config IESO         = OFF                               // Internal/external clock switchover
    #pragma config FCKSM        = CSDCMD                            // Clock switching (CSx)/Clock monitor (CMx)
    #pragma config OSCIOFNC     = OFF                               // Clock output on OSCO pin enable

    //*    Other Peripheral Device settings
    #pragma config FWDTEN       = OFF                               // Watchdog timer enable
    #pragma config WDTPS        = PS1024                            // Watchdog timer postscaler

    //*    Code Protection settings
    #pragma config CP           = OFF                               // Code protection
    #pragma config BWP          = OFF                               // Boot flash write protect
    #pragma config PWP          = OFF                               // Program flash write protect

    //*    Debug settings
    #pragma config ICESEL       = ICS_PGx1                          // ICE pin selection

    //*    Other Peripheral Device settings
    #pragma config FSRSSEL      = PRIORITY_7                        // SRS interrupt priority
    #pragma config FCANIO       = OFF                               // Standard/alternate CAN pin select (OFF=Alt)
    #pragma config FETHIO       = ON                                // Standard/alternate ETH pin select (OFF=Alt)
    #pragma config FMIIEN       = OFF                               // MII/RMII select (OFF=RMII)

    //*    USB Settings
    #pragma config UPLLEN       = ON                                // USB PLL enable
    #pragma config UPLLIDIV     = DIV_2                             // USB PLL input divider
    #pragma config FVBUSONIO    = OFF                               // VBUS pin control
    #pragma config FUSBIDIO     = OFF                               // USBID pin control
#endif

    #define CAPABILITIES    (blCapBootLED | blCapDownloadLED | blCapUARTInterface | blCapAutoResetListening | blCapVirtualProgramButton | CAPCOMMON)

    // BTN / LED sense
    #define LedOn       High
    #define BntOn       High

    // Boot LED
    #define BLedLat     G
    #define BLedBit     12

    // Download LED
    #define DLedLat     G
    #define DLedBit     13

    // Virtual program button
    #define VPBntLat    C
    #define VPBntBit    12

    // Other capabilities
    #define LISTEN_BEFORE_LOAD          2000                // no less than 2 seconds
    #define BOOTLOADER_UART             1                   // avrdude program UART
    #define BAUDRATE                    115200              // avrdude baudrate

    #define _CPU_NAME_                  "32MX795F512L"
    #define VEND                        vendDigilent
    #define PROD                        prodCerebotMX7cK
    #define F_CPU                       80000000UL
    #define F_PBUS                      F_CPU

    #define FLASH_BYTES                 0x80000                 // 512K
    #define FLASH_PAGE_SIZE             4096
    #define LoadFlashWaitStates()       (CHECON = 2)            // 0 for 0-30Mhz, 1 for 31-60Mhz, 2 for 61-80Mhz

//************************************************************************
#elif defined(_BOARD_UBW32_MX795_USB_)

#if defined(PUT_CONFIG_BITS_HERE)

    //*    Oscillator Settings
    #pragma config FNOSC        = PRIPLL                            // Oscillator selection
    #pragma config POSCMOD      = XT                                // Primary oscillator mode
    #pragma config FPLLIDIV     = DIV_2                             // PLL input divider
    #pragma config FPLLMUL      = MUL_20                            // PLL multiplier
    #pragma config FPLLODIV     = DIV_1                             // PLL output divider
    #pragma config FPBDIV       = DIV_1                             // Peripheral bus clock divider
    #pragma config FSOSCEN      = OFF                               // Secondary oscillator enable

    //*    Clock control settings
    #pragma config IESO         = ON                                // Internal/external clock switchover
    #pragma config FCKSM        = CSDCMD                            // Clock switching (CSx)/Clock monitor (CMx)
    #pragma config OSCIOFNC     = OFF                               // Clock output on OSCO pin enable

    //*    Other Peripheral Device settings
    #pragma config FWDTEN       = OFF                               // Watchdog timer enable
    #pragma config WDTPS        = PS1024                            // Watchdog timer postscaler

    //*    Code Protection settings
    #pragma config CP           = OFF                               // Code protection
    #pragma config BWP          = OFF                               // Boot flash write protect
    #pragma config PWP          = OFF                               // Program flash write protect

    //*    Debug settings
    #pragma config ICESEL       = ICS_PGx2                          // ICE pin selection

    //*    Other Peripheral Device settings
    #pragma config FSRSSEL      = PRIORITY_7                        // SRS interrupt priority
    #pragma config FCANIO       = OFF                               // Standard/alternate CAN pin select (OFF=Alt)
    #pragma config FETHIO       = ON                                // Standard/alternate ETH pin select (OFF=Alt)
    #pragma config FMIIEN       = OFF                               // MII/RMII select (OFF=RMII)

    //*    USB Settings
    #pragma config UPLLEN       = ON                                // USB PLL enable
    #pragma config UPLLIDIV     = DIV_2                             // USB PLL input divider
    #pragma config FVBUSONIO    = OFF                               // VBUS pin control
    #pragma config FUSBIDIO     = OFF                               // USBID pin control
#endif

    #define CAPABILITIES    (blCapBootLED | blCapDownloadLED | blCapUSBInterface | blCapProgramButton | blCapVirtualProgramButton | CAPCOMMON)

    // BTN / LED sense
    #define LedOn       High
    #define BntOn       Low

    // Boot LED
    #define BLedLat     E
    #define BLedBit     3

    // Download LED
    #define DLedLat     E
    #define DLedBit     2

    // Virtual program button
    #define VPBntLat    E
    #define VPBntBit    7

    // Program button
    #define PBntPort    E
    #define PBntBit     7

    #define _CPU_NAME_                  "32MX795F512L"
    #define VEND                        vendSchmalzHausLLC
    #define PROD                        prodUBW32MX795
    #define F_CPU                       80000000UL
    #define F_PBUS                      F_CPU

    #define FLASH_BYTES                 0x80000                     // 512K
    #define FLASH_PAGE_SIZE             4096
    #define LoadFlashWaitStates()       (CHECON = 2)                // 0 for 0-30Mhz, 1 for 31-60Mhz, 2 for 61-80Mhz

//************************************************************************
#elif defined(_BOARD_CHIPKIT_FG32_)

#if defined(PUT_CONFIG_BITS_HERE)

    //*    Oscillator Settings
    #pragma config FNOSC        = PRIPLL                            // Oscillator selection
    #pragma config POSCMOD      = XT                                // Primary oscillator mode
    #pragma config FPLLIDIV     = DIV_2                             // PLL input divider
    #pragma config FPLLMUL      = MUL_20                            // PLL multiplier
    #pragma config FPLLODIV     = DIV_1                             // PLL output divider
    #pragma config FPBDIV       = DIV_1                             // Peripheral bus clock divider
    #pragma config FSOSCEN      = OFF                               // Secondary oscillator enable

    //*    Clock control settings
    #pragma config IESO         = OFF                               // Internal/external clock switchover
    #pragma config FCKSM        = CSDCMD                            // Clock switching (CSx)/Clock monitor (CMx)
    #pragma config OSCIOFNC     = OFF                               // Clock output on OSCO pin enable

    //*    Other Peripheral Device settings
    #pragma config FWDTEN       = OFF                               // Watchdog timer enable
    #pragma config WDTPS        = PS1024                            // Watchdog timer postscaler

    //*    Code Protection settings
    #pragma config CP           = OFF                               // Code protection
    #pragma config BWP          = OFF                               // Boot flash write protect
    #pragma config PWP          = OFF                               // Program flash write protect

    //*    Debug settings
    #pragma config ICESEL       = ICS_PGx2                          // ICE pin selection

    //*    Other Peripheral Device settings
    #pragma config FSRSSEL      = PRIORITY_7                        // SRS interrupt priority
    #pragma config FCANIO       = OFF                               // Standard/alternate CAN pin select (OFF=Alt)
    #pragma config FETHIO       = ON                                // Standard/alternate ETH pin select (OFF=Alt)
    #pragma config FMIIEN       = OFF                               // MII/RMII select (OFF=RMII)

    //*    USB Settings
    #pragma config UPLLEN       = ON                                // USB PLL enable
    #pragma config UPLLIDIV     = DIV_2                             // USB PLL input divider
    #pragma config FVBUSONIO    = OFF                               // VBUS pin control
    #pragma config FUSBIDIO     = OFF                               // USBID pin control
#endif

    #define CAPABILITIES    (blCapUARTInterface | blCapAutoResetListening | blCapVirtualProgramButton | CAPCOMMON)

    // BTN / LED sense
    #define LedOn       High
    #define BntOn       High

    // Boot LED
//    #define BLedLat     A
//    #define BLedBit     3

    // Download LED
//    #define DLedLat     C
//    #define DLedBit     1

    // Virtual program button
    #define VPBntLat    C
    #define VPBntBit    12

    // Other capabilities
    #define LISTEN_BEFORE_LOAD          2000                // no less than 2 seconds
    #define BOOTLOADER_UART             1                   // avrdude program UART
    #define BAUDRATE                    115200              // avrdude baudrate

    #define _CPU_NAME_                  "32MX695F512L"
    #define VEND                        vendDigilent
    #define PROD                        prodChipKITFG32
    #define F_CPU                       80000000UL
    #define F_PBUS                      F_CPU

    #define FLASH_BYTES                 0x80000                     // 512K
    #define FLASH_PAGE_SIZE             4096
    #define LoadFlashWaitStates()       (CHECON = 2)                // 0 for 0-30Mhz, 1 for 31-60Mhz, 2 for 61-80Mhz

//************************************************************************
#elif defined(_BOARD_FUBARINO_SD_USB_)  // 32MX440F256H, SeedStudio version (after first 100) - v1.4
 
#if defined(PUT_CONFIG_BITS_HERE)

    //* Oscillator Settings
    #pragma config FNOSC    = PRIPLL                                // Oscillator selection
    #pragma config POSCMOD  = HS                                    // Primary oscillator mode
    #pragma config FPLLIDIV = DIV_2                                 // PLL input divider
    #pragma config FPLLMUL  = MUL_20                                // PLL multiplier
    #pragma config FPLLODIV = DIV_1                                 // PLL output divider
    #pragma config FPBDIV   = DIV_1                                 // Peripheral bus clock divider
    #pragma config FSOSCEN  = OFF                                   // Secondary oscillator enable
    
    //* Clock control settings
    #pragma config IESO     = OFF                                   // Internal/external clock switchover
    #pragma config FCKSM    = CSECME                                // Clock switching (CSx)/Clock monitor (CMx)
    #pragma config OSCIOFNC = OFF                                   // Clock output on OSCO pin enable
    
    //* USB Settings
    #pragma config UPLLEN   = ON                                    // USB PLL enable
    #pragma config UPLLIDIV = DIV_2                                 // USB PLL input divider
    
    //* Other Peripheral Device settings
    #pragma config FWDTEN   = OFF                                   // Watchdog timer enable
    #pragma config WDTPS    = PS1024                                // Watchdog timer postscaler
    
    //* Code Protection settings
    #pragma config CP       = OFF                                   // Code protection
    #pragma config BWP      = OFF                                   // Boot flash write protect
    #pragma config PWP      = OFF                                   // Program flash write protect
    
    //* Debug settings
    #pragma config ICESEL   = ICS_PGx2                              // ICE pin selection
#endif
    
    #define CAPABILITIES    (blCapBootLED | blCapUSBInterface | blCapProgramButton | blCapVirtualProgramButton | CAPCOMMON)

    // BTN / LED sense
    #define LedOn       High
    #define BntOn       Low

    // Boot LED
    #define BLedLat     E
    #define BLedBit     5

    // Virtual program button
    #define VPBntLat    E
    #define VPBntBit    7

    // Program button
    #define PBntPort    E
    #define PBntBit     7
 
    #define _CPU_NAME_                  "32MX440F256H"
    #define VEND                        vendFubarino
    #define PROD                        prodFubarinoSD
    #define F_CPU                       80000000UL
    #define F_PBUS                      F_CPU

    #define FLASH_BYTES                 0x40000                     // 256K
    #define FLASH_PAGE_SIZE             4096
    #define LoadFlashWaitStates()       (CHECON = 2)            // 0 for 0-30Mhz, 1 for 31-60Mhz, 2 for 61-80Mhz

//************************************************************************
#elif defined(_BOARD_FUBARINO_SD_512K_USB_) // 32MX795F512H, Microchip version (v1.5)

#if defined(PUT_CONFIG_BITS_HERE)

    //* Oscillator Settings
    #pragma config FNOSC    = PRIPLL                                // Oscillator selection
    #pragma config POSCMOD  = HS                                    // Primary oscillator mode
    #pragma config FPLLIDIV = DIV_2                                 // PLL input divider
    #pragma config FPLLMUL  = MUL_20                                // PLL multiplier
    #pragma config FPLLODIV = DIV_1                                 // PLL output divider
    #pragma config FPBDIV   = DIV_1                                 // Peripheral bus clock divider
    #pragma config FSOSCEN  = OFF                                   // Secondary oscillator enable

    //* Clock control settings
    #pragma config IESO     = OFF                                   // Internal/external clock switchover
    #pragma config FCKSM    = CSECME                                // Clock switching (CSx)/Clock monitor (CMx)
    #pragma config OSCIOFNC = OFF                                   // Clock output on OSCO pin enable

    //* USB Settings
    #pragma config UPLLEN   = ON                                    // USB PLL enable
    #pragma config UPLLIDIV = DIV_2                                 // USB PLL input divider
    #pragma config FUSBIDIO = OFF									// USB USID pin controlled by port function
    #pragma config FVBUSONIO = OFF									// USB VBUSON pin controlled by port function

    //* Other Peripheral Device settings
    #pragma config FWDTEN   = OFF                                   // Watchdog timer enable
    #pragma config WDTPS    = PS1024                                // Watchdog timer postscaler

    //* Code Protection settings
    #pragma config CP       = OFF                                   // Code protection
    #pragma config BWP      = OFF                                   // Boot flash write protect
    #pragma config PWP      = OFF                                   // Program flash write protect

    //* Debug settings
    #pragma config ICESEL   = ICS_PGx2                              // ICE pin selection
#endif

    #define CAPABILITIES    (blCapBootLED | blCapUSBInterface | blCapProgramButton | blCapVirtualProgramButton | CAPCOMMON)

    // BTN / LED sense
    #define LedOn       High
    #define BntOn       Low

    // Boot LED
    #define BLedLat     E
    #define BLedBit     5

    // Virtual program button
    #define VPBntLat    E
    #define VPBntBit    7

    // Program button
    #define PBntPort    E
    #define PBntBit     7
 
    #define _CPU_NAME_                  "32MX795F512H"
    #define VEND                        vendFubarino
    #define PROD                        prodFubarinoSD_512K
    #define F_CPU                       80000000UL
    #define F_PBUS                      F_CPU

    #define FLASH_BYTES                 0x80000                     // 512K
    #define FLASH_PAGE_SIZE             4096
    #define LoadFlashWaitStates()       (CHECON = 2)            // 0 for 0-30Mhz, 1 for 31-60Mhz, 2 for 61-80Mhz

//************************************************************************
#elif defined(_BOARD_FUBARINO_MINI_USB_)
 
#if defined(PUT_CONFIG_BITS_HERE)

    //* Oscillator Settings
    #pragma config FNOSC    = PRIPLL                                // Oscillator selection
    #pragma config POSCMOD  = XT                                    // Primary oscillator mode
    #pragma config FPLLIDIV = DIV_2                                 // PLL input divider
    #pragma config FPLLMUL  = MUL_20                                // PLL multiplier
    #pragma config FPLLODIV = DIV_2                                 // PLL output divider
    #pragma config FPBDIV   = DIV_1                                 // Peripheral bus clock divider
    #pragma config FSOSCEN  = OFF                                   // Secondary oscillator enable
    
    //* Clock control settings
    #pragma config IESO     = OFF                                   // Internal/external clock switchover
    #pragma config FCKSM    = CSECME                                // Clock switching (CSx)/Clock monitor (CMx)
    #pragma config OSCIOFNC = OFF                                   // Clock output on OSCO pin enable
    
    //* USB Settings
    #pragma config UPLLEN   = ON                                    // USB PLL enable
    #pragma config UPLLIDIV = DIV_2                                 // USB PLL input divider
    #pragma config FUSBIDIO = OFF									// USB USID pin controlled by port function
    #pragma config FVBUSONIO = OFF									// USB VBUSON pin controlled by port function
    
    //* Other Peripheral Device settings
    #pragma config FWDTEN   = OFF                                   // Watchdog timer enable
    #pragma config WDTPS    = PS1024                                // Watchdog timer postscaler
    #pragma config WINDIS   = OFF
    #pragma config JTAGEN   = OFF                          			// JTAG port disabled
    
    //* Code Protection settings
    #pragma config CP       = OFF                                   // Code protection
    #pragma config BWP      = OFF                                   // Boot flash write protect
    #pragma config PWP      = OFF                                   // Program flash write protect
    
    //*    Debug settings
    #pragma config ICESEL   = ICS_PGx1                      		// ICE/ICD Comm Channel Select
    //#pragma config DEBUG    = ON                          		// DO NOT SET THIS CONFIG BIT, it will break debugging

    #pragma config PMDL1WAY = OFF                           		// Allow multiple reconfigurations
    #pragma config IOL1WAY  = OFF                           		// Allow multiple reconfigurations
#endif
    
    #define CAPABILITIES    (blCapBootLED | blCapSplitFlashBootloader | blCapUSBInterface | blCapProgramButton | blCapVirtualProgramButton | CAPCOMMON)

    // BTN / LED sense
    #define LedOn       High
    #define BntOn       Low

    // Boot LED
    #define BLedLat     A
    #define BLedBit     10

    // Virtual program button
    #define VPBntLat    A
    #define VPBntBit    8

    // Program button
    #define PBntPort    A
    #define PBntBit     8
  
    #define _CPU_NAME_                  "32MX250F128D"
    #define VEND                        vendFubarino
    #define PROD                        prodFubarinoMini
    #define F_CPU                       40000000UL
    #define F_PBUS                      F_CPU

    #define FLASH_BYTES                 (0x20000-0x1000)		    // Leave room one flash block (for bootloader!)
    #define FLASH_PAGE_SIZE             1024						// In bytes

//************************************************************************
#elif defined(_BOARD_FUBARINO_MINI_USB_48MHZ_)
 
#if defined(PUT_CONFIG_BITS_HERE)

    //* Oscillator Settings
    #pragma config FNOSC    = PRIPLL                                // Oscillator selection
    #pragma config POSCMOD  = XT                                    // Primary oscillator mode
    #pragma config FPLLIDIV = DIV_2                                 // PLL input divider
    #pragma config FPLLMUL  = MUL_24                                // PLL multiplier
    #pragma config FPLLODIV = DIV_2                                 // PLL output divider
    #pragma config FPBDIV   = DIV_1                                 // Peripheral bus clock divider
    #pragma config FSOSCEN  = OFF                                   // Secondary oscillator enable
    
    //* Clock control settings
    #pragma config IESO     = OFF                                   // Internal/external clock switchover
    #pragma config FCKSM    = CSECME                                // Clock switching (CSx)/Clock monitor (CMx)
    #pragma config OSCIOFNC = OFF                                   // Clock output on OSCO pin enable
    
    //* USB Settings
    #pragma config UPLLEN   = ON                                    // USB PLL enable
    #pragma config UPLLIDIV = DIV_2                                 // USB PLL input divider
    #pragma config FUSBIDIO = OFF									// USB USID pin controlled by port function
    #pragma config FVBUSONIO = OFF									// USB VBUSON pin controlled by port function
    
    //* Other Peripheral Device settings
    #pragma config FWDTEN   = OFF                                   // Watchdog timer enable
    #pragma config WDTPS    = PS1024                                // Watchdog timer postscaler
    #pragma config WINDIS   = OFF
    #pragma config JTAGEN   = OFF                          			// JTAG port disabled
    
    //* Code Protection settings
    #pragma config CP       = OFF                                   // Code protection
    #pragma config BWP      = OFF                                   // Boot flash write protect
    #pragma config PWP      = OFF                                   // Program flash write protect
    
    //*    Debug settings
    #pragma config ICESEL   = ICS_PGx1                      		// ICE/ICD Comm Channel Select
    //#pragma config DEBUG    = ON                          		// DO NOT SET THIS CONFIG BIT, it will break debugging

    #pragma config PMDL1WAY = OFF                           		// Allow multiple reconfigurations
    #pragma config IOL1WAY  = OFF                           		// Allow multiple reconfigurations
#endif
    
    #define CAPABILITIES    (blCapBootLED | blCapSplitFlashBootloader | blCapUSBInterface | blCapProgramButton | blCapVirtualProgramButton | CAPCOMMON)

    // BTN / LED sense
    #define LedOn       High
    #define BntOn       Low

    // Boot LED
    #define BLedLat     A
    #define BLedBit     10


    // Virtual program button
    #define VPBntLat    A
    #define VPBntBit    8

    // Program button
    #define PBntPort    A
    #define PBntBit     8
  
    #define _CPU_NAME_                  "32MX250F128D"
    #define VEND                        vendFubarino
    #define PROD                        prodFubarinoMini48MHz
    #define F_CPU                       48000000UL
    #define F_PBUS                      F_CPU

    #define FLASH_BYTES                 (0x20000-0x1000)		    // Leave room one flash block (for bootloader!)
    #define FLASH_PAGE_SIZE             1024						// In bytes

//************************************************************************
#elif defined(_BOARD_FUBARINO_MINI_USB_50MHZ_)
// This is a Fubarino Mini with a 20MHz crystal
 
#if defined(PUT_CONFIG_BITS_HERE)

    //* Oscillator Settings
    #pragma config FNOSC    = PRIPLL                                // Oscillator selection
    #pragma config POSCMOD  = XT                                    // Primary oscillator mode
    #pragma config FPLLIDIV = DIV_4                                 // PLL input divider
    #pragma config FPLLMUL  = MUL_20                                // PLL multiplier
    #pragma config FPLLODIV = DIV_2                                 // PLL output divider
    #pragma config FPBDIV   = DIV_1                                 // Peripheral bus clock divider
    #pragma config FSOSCEN  = OFF                                   // Secondary oscillator enable
    
    //* Clock control settings
    #pragma config IESO     = OFF                                   // Internal/external clock switchover
    #pragma config FCKSM    = CSECME                                // Clock switching (CSx)/Clock monitor (CMx)
    #pragma config OSCIOFNC = OFF                                   // Clock output on OSCO pin enable
    
    //* USB Settings
    #pragma config UPLLEN   = ON                                    // USB PLL enable
    #pragma config UPLLIDIV = DIV_5                                 // USB PLL input divider
    #pragma config FUSBIDIO = OFF									// USB USID pin controlled by port function
    #pragma config FVBUSONIO = OFF									// USB VBUSON pin controlled by port function
    
    //* Other Peripheral Device settings
    #pragma config FWDTEN   = OFF                                   // Watchdog timer enable
    #pragma config WDTPS    = PS1024                                // Watchdog timer postscaler
    #pragma config WINDIS   = OFF
    #pragma config JTAGEN   = OFF                          			// JTAG port disabled
    
    //* Code Protection settings
    #pragma config CP       = OFF                                   // Code protection
    #pragma config BWP      = OFF                                   // Boot flash write protect
    #pragma config PWP      = OFF                                   // Program flash write protect
    
    //*    Debug settings
    #pragma config ICESEL   = ICS_PGx1                      		// ICE/ICD Comm Channel Select
    //#pragma config DEBUG    = ON                          		// DO NOT SET THIS CONFIG BIT, it will break debugging

    #pragma config PMDL1WAY = OFF                           		// Allow multiple reconfigurations
    #pragma config IOL1WAY  = OFF                           		// Allow multiple reconfigurations
#endif
    
    #define CAPABILITIES    (blCapBootLED | blCapSplitFlashBootloader | blCapUSBInterface | blCapProgramButton | blCapVirtualProgramButton | CAPCOMMON)

    // BTN / LED sense
    #define LedOn       High
    #define BntOn       Low

    // Boot LED
    #define BLedLat     A
    #define BLedBit     10

    // Virtual program button
    #define VPBntLat    A
    #define VPBntBit    8

    // Program button
    #define PBntPort    A
    #define PBntBit     8
 
    #define _CPU_NAME_                  "32MX250F128D"
    #define VEND                        vendFubarino
    #define PROD                        prodFubarinoMini50MHz
    #define F_CPU                       50000000UL
    #define F_PBUS                      F_CPU

    #define FLASH_BYTES                 (0x20000-0x1000)		    // Leave room one flash block (for bootloader!)
    #define FLASH_PAGE_SIZE             1024						// In bytes

//************************************************************************
#elif defined(_BOARD_OLIMEX_PIC32_PINGUINO_)
 
#if defined(PUT_CONFIG_BITS_HERE)

    //* Oscillator Settings
    #pragma config FNOSC    = PRIPLL                                // Oscillator selection
    #pragma config POSCMOD  = HS                                    // Primary oscillator mode
    #pragma config FPLLIDIV = DIV_2                                 // PLL input divider
    #pragma config FPLLMUL  = MUL_20                                // PLL multiplier
    #pragma config FPLLODIV = DIV_1                                 // PLL output divider
    #pragma config FPBDIV   = DIV_1                                 // Peripheral bus clock divider
    #pragma config FSOSCEN  = OFF                                   // Secondary oscillator enable
    
    //* Clock control settings
    #pragma config IESO     = OFF                                   // Internal/external clock switchover
    #pragma config FCKSM    = CSECME                                // Clock switching (CSx)/Clock monitor (CMx)
    #pragma config OSCIOFNC = OFF                                   // Clock output on OSCO pin enable
    
    //* USB Settings
    #pragma config UPLLEN   = ON                                    // USB PLL enable
    #pragma config UPLLIDIV = DIV_2                                 // USB PLL input divider
    
    //* Other Peripheral Device settings
    #pragma config FWDTEN   = OFF                                   // Watchdog timer enable
    #pragma config WDTPS    = PS1024                                // Watchdog timer postscaler
    #pragma config WINDIS   = OFF
    #pragma config JTAGEN   = OFF                          			// JTAG port disabled
   
    //* Code Protection settings
    #pragma config CP       = OFF                                   // Code protection
    #pragma config BWP      = OFF                                   // Boot flash write protect
    #pragma config PWP      = OFF                                   // Program flash write protect
    
    //* Debug settings
    #pragma config ICESEL   = ICS_PGx2                              // ICE pin selection
    //#pragma config DEBUG    = ON                          		// DO NOT SET THIS CONFIG BIT, it will break debugging
#endif
    
    #define CAPABILITIES    (blCapBootLED | blCapSplitFlashBootloader | blCapUSBInterface | blCapProgramButton | blCapVirtualProgramButton | CAPCOMMON)

    // BTN / LED sense
    #define LedOn       High
    #define BntOn       Low

    // Boot LED
    #define BLedLat     G
    #define BLedBit     6

    // Virtual program button
    #define VPBntLat    D
    #define VPBntBit    0

    // Program button
    #define PBntPort    D
    #define PBntBit     0
 
    #define _CPU_NAME_                  "32MX440F256H"
    #define VEND                        vendOlimex
    #define PROD                        prodOlimex_PIC32_Pinguino
    #define F_CPU                       80000000UL
    #define F_PBUS                      F_CPU

    #define FLASH_BYTES                 0x40000                     // 256K
    #define FLASH_PAGE_SIZE             4096
    #define LoadFlashWaitStates()       (CHECON = 2)            // 0 for 0-30Mhz, 1 for 31-60Mhz, 2 for 61-80Mhz

//************************************************************************
#elif defined(_BOARD_EBBV3_USB_)
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
